dumaiss/Zephyr-80/Code/HOST/CPM2.2/docs/memory-map.md

# Zephyr-80 CP/M 2.2 Memory Map

Generated by `tools/generate_memory_docs.py` from `build/firmware.lst`, `src/layout/memory.inc`, `build/layout.manifest` and the image artifacts. Do not edit by hand; `make` regenerates it and fails if the layout breaks a rule below.

The operating system runs from SRAM bank 7, visible at `2000h-DFFFh` only in latch mode 11. Common memory, `E000h-FFFFh`, is SRAM bank 0 in both modes. See `docs/Zephyr-80_OS_Execution_Memory_Architecture.md` for the design.

## What a Program Sees (mode 10)

| Range | Use |
|---|---|
| `0000h-00FFh` | Page zero, default FCBs and default DMA, in the program's bank |
| `0100h-DFFFh` | Banked transient program area |
| `E000h-E3FFh` | Program reservation: interrupt callbacks and their data |
| `E400h-EBFFh` | CCP (ZCPR2), restored on warm boot |
| `EC00h-EC05h` | BDOS serial number |
| `EC06h` | `FBASE`, the BDOS entry |
| `F000h-FFFFh` | System common memory |

Page zero's `0006h` holds `EC06h`: the transient program area is `0100h-EC05h`, 60166 bytes (58.8 KiB).

## Common Memory

Code regions, each bounded by the limit `cbios_defs.inc` declares for it. Used and free are bytes.

| Region | Owner | Zone | Used | Free | Contents |
|---|---|---|---:|---:|---|
| `EC00h-EF9Fh` | BDOS facade | abi | 928 | 0 | `CALL 5`: serial number, `FBASE`, argument staging, Zephyr functions 200-218, system information block. |
| `EFA0h-EFB0h` | IOC link failure record | abi | 16 | 1 | Read by the CP/M tools through BDOS function 203. |
| `EFB1h-EFF7h` | Destructive COM loader | abi | 66 | 5 | Private BDOS 219: 512-byte native load, supervisor commit and close, jump to 0100h. |
| `EFF8h-EFFFh` | Transport level | abi | 1 | 7 | The BIOS IO Controller transport level byte. |
| `F000h-F1AFh` | BIOS tables, ROM copy, boot | abi | 425 | 7 | CP/M BIOS table, Zephyr extension table, reset copy, cold boot, warm-boot teardown, supervisor entry glue, page zero. |
| `F1B0h-F1D1h` | SIO ownership return | crossing | 34 | 0 | Quiesces application-owned SIO0/A at boot and application exit. |
| `F1D2h-F20Fh` | Native file gate | crossing | 46 | 16 | Function 218 descriptor and read-data staging through the existing crossing mechanism. |
| `F210h-F2E7h` | Banking services | crossing | 210 | 6 | `SELMEM`, `SETBNK`, `XMOVE`, `MOVE`. |
| `F2E8h-F307h` | Crossing layer | crossing | 26 | 6 | Mode-preserving bank select; SIO IM2 entry belongs to the IRQ core. |
| `F308h-F4EFh` | Crossing gates | crossing | 476 | 12 | Console and IOC/video gates into bank 7, inert disk entries, warm-boot trap, ROM-disk copy window, bank 7 check. |
| `F4F0h-F4FFh` | CTC reset | interrupt | 15 | 1 | `ctc_disable_interrupts`: CTC reset and vector base. |
| `F500h-F65Fh` | SIO core | interrupt | 330 | 22 | SIO0/B and SIO1 initialization, receive sinks, SIO interrupt body. |
| `F660h-F757h` | Interrupt dispatch | interrupt | 189 | 59 | CTC/SIO entries, complete context preservation, dispatch and boot policy. |
| `F758h-F79Fh` | IRQ policy | interrupt | 64 | 8 | Interrupt tokens, stackless boot policy and polling context preservation. |
| `F7A0h-F7BFh` | CTC channel mapping | interrupt | 21 | 11 | Logical-channel stop using the platform port mapping. |
| `F7C0h-F84Fh` | IRQ registration | interrupt | 121 | 23 | Atomic user/kernel callback registration. |
| `F850h-F9FFh` | Serial console | driver-isr | 84 | 348 | Serial console tee and input switch. |

Data and stacks:

| Range | Use | Notes |
|---|---|---|
| `FA00h-FBFFh` | Staging buffer | 512 bytes, shared by facade DMA/FCB/console/time staging, gate mailboxes and payloads, and cross-bank `MOVE` chunks. Users never overlap in time. |
| `FF60h (empty)` | Facade copies | Search-first FCB, DPB copy (function 31), register block (functions 210-217), ALV copy (function 27). |
| `FD00h-FDFFh` | IM2 vector page | `I` = `FDh`; programmed even entries point into common memory. |
| `FE00h` | IM2 `FFh` guard | Second byte of the pointer fetched at `FDFFh`; completes the safe `F6F6h` target. |
| `FE01h-FE7Fh` | BIOS runtime state | Bank, DMA, console, banking, storage, SIO and serial console state. |
| `FE80h-FE81h` | Interrupted SP | Saved by every interrupt entry. |
| `FE82h-FEBFh` | ISR stack | SIO and CTC interrupts; registered callbacks run here. |
| `FEC0h-FEFFh` | Gate stack | Program calls through the crossing gates. |
| `FF00h-FF5Fh` | Facade stack | BDOS facade, warm-boot trap, final boot switch to mode 10. |

System common code ends at `F8A3h`.

## SRAM Bank 7 (mode 11 only)

| Region | Owner | Zone | Used | Free | Contents |
|---|---|---|---:|---:|---|
| `2000h-2FFFh` | ZSDOS | core | — | — | Installed from `build/bdos-zsdos.bin` by `tools/split_banked_image.py`. |
| `3000h-31FFh` | ZSDOS's BIOS table | core | 59 | 453 | The table ZSDOS calls, and the `BANK7OS1` image marker. |
| `3200h-33FFh` | Console facade | core | 125 | 387 | CP/M console entries; dispatch on the console stack. |
| `3400h-35FFh` | Storage facade | core | 26 | 486 | CP/M disk entries; jumps into the drive dispatcher. |
| `3600h-37FFh` | VIDEO_SEND | core | 40 | 472 | Raw video request through the selected console backend. |
| `3800h-39FFh` | IOCALL | core | 140 | 372 | 32-byte mailbox transaction. |
| `3A00h-41FFh` | IOC command lane | driver | 1037 | 1011 | Common-packet command-lane transport. |
| `4200h-43FFh` | Bulk entries | core | 43 | 469 | `IOCBULK` and `IOCBULKW`. |
| `4400h-49FFh` | IOC bulk lane | driver | 558 | 978 | Common-packet bulk-lane transport and link bring-up. |
| `4A00h-4BFFh` | USB keyboard input | driver | 186 | 326 | Doorbell-gated keyboard fetch. |
| `4C00h-4DFFh` | USB keyboard state | state | 57 | 455 | Mailboxes and keyboard queue. |
| `4E00h-53FFh` | SD-card backend | driver | 745 | 791 | Record read and write through the IO Controller cache. |
| `5400h-55FFh` | B: select probe | driver | 23 | 489 | Card availability, then the B: DPH. |
| `5600h-57FFh` | Drive A: backend | driver | 164 | 348 | The build-selected A: backend. |
| `5800h-59FFh` | Drive dispatcher | core | 179 | 333 | Routes A: to its backend, gated B: to the synthetic FAT BIOS, and C:/D: to SD units. |
| `5A00h-5FFFh` | CP/M A: mount provider | driver | 1192 | 344 | Read-only CP/M directory/extent adapter behind function 218 at `/SYSTEM/A`. |
| `8000h-87FFh` | Console font | asset | 2048 | 0 | Build-selected CP850 glyph source, read once at boot. |
| `8800h-8BFFh` | Boot banner text | asset | 64 | 960 | Banner string, CP850 to match the console atlas. |
| `8C00h-8FFFh` | Boot banner printer | asset | 56 | 968 | Prints the banner text beside it; runs once from cold boot, in mode 11. |
| `9000h-9FFFh` | V9958 console | driver | 3208 | 888 | Direct LunchCrema V9958 console: parser, renderer, cursor and state. |
| `A000h-B7FFh` | FAT BDOS backend | driver | 5768 | 376 | FS2 client, native file manager, writable FAT BDOS personality, read cache, DPH and DPB. |
| `B800h-B9FFh` | SIO services (bank 7) | core | 121 | 391 | `sio1_ioc_init`, `sio_core_enable_interrupts`, `sio_register_rx_sink`: reached only from bank 7 or from boot after `bank7_check`. |
| `BA00h-BBFFh` | Serial console tee (bank 7) | driver | 211 | 301 | Driver table, init/install, the CONST/CONIN/CONOUT tee and TX; polled through the console facade. |
| `BE00h-BFFFh` | Transient supervisor | core | 104 | 408 | Single-foreground lifecycle policy: next program after cold boot and WBOOT teardown, default shell launch, BDOS 219 child commit. |

Data:

| Range | Use | Notes |
|---|---|---|
| `6000h` | Drive A: DPH and DPB | Build-selected A: backend. |
| `6020h` | B: DPH and DPB | SD unit 0. |
| `6040h` | Directory buffer | Shared by every drive. |
| `6100h` | Drive A: allocation vector | |
| `6300h` | B: allocation vector | |
| `6400h` | C: allocation vector | |
| `6500h` | C: DPH and DPB | SD unit 1. |
| `6510h-65FFh` | Unallocated | Deliberate gap after the C: DPH. |
| `6600h-7FFFh` | Reclaimable resource/cache pool | 13 lines of 512 bytes; no permanent owner. |
| `8000h-87FFh` | Console font | CP850 6x8. |
| `8800h-883Fh` | Boot banner text | |
| `A04Ah` | B: synthetic DPH and DPB | Read-only FAT compatibility geometry; selection gate is `1`. |

The last resident asset ends at `D649h`. Cold boot installs all 64 KiB; OS-owned initialized contents may occupy `C000h-DFFFh` outside the reservations below.

| Range | Use |
|---|---|
| `C000h-C0FFh` | Boot and warm-boot stack |
| `C100h-C1FFh` | Console and storage dispatch stack |
| `C200h-C2FFh` | IO Controller transport stack |
| `C300h-C3BFh` | SD transaction scratch (`MOVE_BUFFER`) |
| `C3C0h-C3FFh` | Unallocated |
| `C400h-CBFFh` | Pristine CCP restore asset |
| `CC00h (empty)` | Unallocated |
| `CC00h-CDFFh` | SD deblock line (one 512-byte logical block) |
| `CE00h-CE08h` | SD deblock tag (valid, unit, block) |
| `CE09h-CE0Fh` | Unallocated |
| `CE10h-D60Fh` | FAT BDOS persistent-state reservation | Fixed bank-7 state; track/sector and synthetic ALV currently use `1131` bytes. |
| `D610h-D70Fh` | CP/M A: mount state | Function-218 provider CWD, handle, iterator and extent-reader state; currently uses `58` bytes. |
| `D710h-D71Fh` | Transient supervisor state | Foreground role, execution policy, flags and layout version; currently uses `4` bytes. Written in full at cold boot. |
| `D720h-DFFFh` | Unallocated |

All eight physical SRAM banks include E000h-FFFFh, visible in flat mode 01. Modes 10/11 overlay that range with bank 0.

## Image

| Bank / page | Payload | Size | Source |
|---:|---|---:|---|
| 0 | Reset vector and common memory | 65536 | `build/firmware.bin` |
| 1 | ROM disk page 1 | 49152 | `build/romdisk.p1.bin` |
| 2 | ROM disk page 2 | 49152 | `build/romdisk.p2.bin` |
| 3 | ROM disk page 3 | 49152 | `build/romdisk.p3.bin` |
| 7 | OS bank 7 | 65536 | `build/bank7.bin` |

The burnable image `build/zephyr80.bin` is 524288 bytes. Console backend: `v9958`. Drive A: backend: `rom`. FAT drive selection gate: `1`.

## Validation Report

Status: PASS.

Checked:

- Every declared region starts at its base symbol and ends at or below its limit.
- Declared regions do not overlap.
- No assembled bytes overlap the caller window beyond the disposable bootstrap, ZSDOS, private stacks/scratch, pristine CCP, program reservation or live CCP.
- Bank 7 resident contents fit below `E000h`; the full 64 KiB boot page is installed.
- `FBASE` is six bytes into the facade, which follows the 2 KiB CCP slot; the facade ends below `CBIOS_BASE`.
- ZSDOS's BIOS table is at `ZSDOS_ORG + ZSDOS_SIZE`, and ends with the `BANK7OS1` marker.
- The CP/M BIOS table and the Zephyr extension table are jumps, in order.
- The IM2 vector page is 256 bytes at `I * 100h`; programmed even vectors and the cross-page `FFh` vector point into common memory.
- Staging buffers stay inside the shared buffer, and the returned copies do not overlap each other or the IM2 page.
- Runtime state blocks stay inside `FE00h-FE7Fh` without overlapping.
- The interrupt, gate and facade stacks are ordered, disjoint and common; the BIOS private stacks and SD scratch lie in bank 7's `C000h-DFFFh`.
- The 13-by-512-byte resource/cache pool remains reclaimable and disjoint from fixed FAT code and persistent state.
- FAT backend code and persistent state remain inside their declared bank-7 ceilings.
- The synthetic FAT DPH points at the shared directory buffer, its fixed DPB, a null CSV and its bank-7 ALV.
