dumaiss/Zephyr-80/Code/HOST/ColecoGo/snap/coleco/0000.png

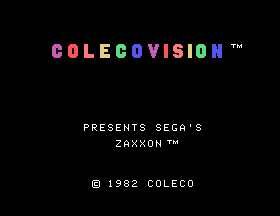
Code/HOST/ColecoGo/snap/coleco/0000.png
