dumaiss/Zephyr-80/Code/MCU/IOController/include/ioc_frame.h

#ifndef IOC_FRAME_H
#define IOC_FRAME_H

#include "sd_card.h"

#include <stdint.h>
#include <stdbool.h>

/* BIOS-facing command mailboxes remain fixed at 32 bytes.  They are no longer
 * the wire format: both SIO lanes use the common variable-length packet below,
 * and the transport maps between that packet and this compatibility mailbox.
 *
 * Layout:
 *   byte 0      class / command / response type
 *   byte 1      sequence number
 *   byte 2      status / flags
 *   byte 3      payload length (consumer-defined)
 *   bytes 4-19  payload (up to 16 bytes)
 *   bytes 20-31 reserved / command-specific
 */
#define IOC_FRAME_SIZE  32

/* Common packet used on BOTH command and bulk lanes:
 *
 *   A5 5A LEN_LO LEN_HI TYPE SEQ STATUS DATA... CRC_HI CRC_LO
 *
 * LEN counts TYPE + SEQ + STATUS + DATA.  STATUS is the first protocol
 * payload byte in both directions; requests send zero.  CRC-16-CCITT uses
 * polynomial 1021h, initial value 0000h, MSB-first processing, no final XOR,
 * and covers LEN_LO through the final DATA byte (not A5 5A).
 *
 * Keeping STATUS in every packet gives the existing mailbox a lossless mapping:
 * bytes 0/1/2 are TYPE/SEQ/STATUS, byte 3 is the derived DATA length, and bytes
 * 4.. are DATA.  Bytes 30/31 are ordinary compatibility-mailbox reserve now;
 * the transport CRC exists only on the wire. */
#define IOC_PACKET_SYNC0           0xA5u
#define IOC_PACKET_SYNC1           0x5Au
#define IOC_PACKET_FIXED_LEN       3u
#define IOC_PACKET_CRC_BYTES       2u
#define IOC_COMMAND_MAX_DATA       (IOC_FRAME_SIZE - IOC_OFF_PAYLOAD - 2u)
#define IOC_COMMAND_MAX_WIRE       (2u + 2u + IOC_PACKET_FIXED_LEN + \
                                    IOC_COMMAND_MAX_DATA + IOC_PACKET_CRC_BYTES)

/* Byte offsets within a frame */
#define IOC_OFF_CLASS    0
#define IOC_OFF_SEQ      1
#define IOC_OFF_STATUS   2
#define IOC_OFF_LEN      3
#define IOC_OFF_PAYLOAD  4

/* READY reply payload, for any command that hands off to the bulk lane.
 * Status is already frame byte 2, so the payload carries the rest:
 *
 *   byte 4  transfer id   (0 means "no transfer")
 *   byte 5  direction     (BULK_DIR_*)
 *   byte 6  length low
 *   byte 7  length high
 */
#define IOC_OFF_READY_XFER_ID    (IOC_OFF_PAYLOAD + 0u)
#define IOC_OFF_READY_DIRECTION  (IOC_OFF_PAYLOAD + 1u)
#define IOC_OFF_READY_LEN_LO     (IOC_OFF_PAYLOAD + 2u)
#define IOC_OFF_READY_LEN_HI     (IOC_OFF_PAYLOAD + 3u)
/* The LBA (or record number) the MCU actually DECODED from the request, echoed
 * back so the host can check it before any data moves.
 *
 * This began as a mitigation for a command lane with no CRC, where a false bit
 * lock could hand a handler a garbage LBA and land a write on a sector nobody
 * asked for -- silently, reporting success.  Observed at the time: the target
 * sector kept its previous contents while the write reported OK.
 *
 * The frame CRC above is now the real fix, and it is checked before dispatch.
 * The echo stays because it is nearly free and it checks a different thing: the
 * CRC proves the frame arrived intact, the echo proves the MCU and the host
 * agree on what the frame MEANT.  A decode bug on either side survives a
 * perfect CRC. */
#define IOC_OFF_READY_LBA        (IOC_OFF_PAYLOAD + 4u)
#define IOC_READY_PAYLOAD_LEN    8u

/* SD_READ_BULK request payload: 32-bit LBA, little-endian. */
#define IOC_OFF_LBA_0            (IOC_OFF_PAYLOAD + 0u)
#define IOC_SD_LBA_PAYLOAD_LEN   4u

/* SD_READ_REC / SD_WRITE_REC request payload: 32-bit CP/M record number, in the
 * same slot as the LBA so one decode path serves both.
 *
 * 8 MiB / 128 = 65536 records, so the volume needs only 16 bits today.  The
 * field is 32 anyway: it sits exactly at the 16-bit ceiling, and widening a
 * protocol field after the fact breaks every .com file already on the disk. */
#define IOC_OFF_RECORD_0         (IOC_OFF_PAYLOAD + 0u)
#define IOC_SD_RECORD_PAYLOAD_LEN 4u
#define IOC_SD_RECORD_BYTES      128u

/* XFER_STATUS REQUEST payload: which part of the raw capture window to return.
 *
 * Eight bytes of window is enough to see that a transfer went wrong and not
 * enough to say how.  A sync failure needs to be told apart three ways -- the
 * host never transmitted, the preamble is present but past the search, or the
 * preamble is corrupt -- and the first eight bytes look similar in all three.
 *
 * Byte 4 of the request is a window offset in bytes.  Zero, which every
 * existing caller sends because they zero the frame, means the same window as
 * before, so this is backward compatible. */
#define IOC_OFF_STATUS_RAW_OFF   (IOC_OFF_PAYLOAD + 0u)

/* XFER_STATUS reply payload: the DONE record. */
#define IOC_OFF_DONE_XFER_ID     (IOC_OFF_PAYLOAD + 0u)
#define IOC_OFF_DONE_STATUS      (IOC_OFF_PAYLOAD + 1u)
/* Bring-up diagnostic: the DONE reply also carries the first few bytes of the
 * transfer buffer, so a write can be checked against what the MCU actually
 * received rather than against what the card reads back afterwards.  That
 * separates "the host never sent it", "the de-shift produced garbage" and "the
 * card write went wrong", which are otherwise indistinguishable. */
#define IOC_OFF_DONE_PEEK        (IOC_OFF_PAYLOAD + 2u)
#define IOC_DONE_PEEK_BYTES      8u
/* Raw capture window, before de-shifting.  With the de-shifted peek above this
 * separates "the host never transmitted" from "the de-shift is wrong": it
 * should contain A5 5A followed by LEN/TYPE/SEQ/STATUS/DATA at some bit phase. */
#define IOC_OFF_DONE_RAW         (IOC_OFF_PAYLOAD + 2u + IOC_DONE_PEEK_BYTES)
#define IOC_DONE_RAW_BYTES       8u
/* Bulk External-Sync discriminator, valid for either transfer direction.
 *
 * DECISION is the state sampled by the most recent MCU->Z80 Bulk send:
 *   bit 0  bulk_synced was set before the send
 *   bit 1  /SYNCA LAT was idle-high before the send
 *   bit 2  the establishing setup/sync-byte path ran
 *   bit 3  /SYNCA LAT was asserted-low after that path
 *
 * LIVE is sampled while building this reply:
 *   bit 0  bulk_synced is currently set
 *   bit 1  /SYNCA LAT is currently asserted-low
 *
 * Together they distinguish a skipped edge (decision 01h), a normal attempted
 * edge (0Eh), and a flag/line disagreement without a logic analyser. */
#define IOC_OFF_DONE_BULK_SYNC_DECISION \
    (IOC_OFF_DONE_RAW + IOC_DONE_RAW_BYTES)
#define IOC_OFF_DONE_BULK_SYNC_LIVE     \
    (IOC_OFF_DONE_BULK_SYNC_DECISION + 1u)
#define IOC_DONE_PAYLOAD_LEN     (4u + IOC_DONE_PEEK_BYTES + IOC_DONE_RAW_BYTES)

/* SD_READ returns this many bytes of the block in the payload area. */
#define IOC_SD_READ_BYTES  16

/* Command class bytes (Z80 → MCU) */
#define CMD_PING             0x01
#define CMD_RESET            0x02
#define CMD_SD_READ          0x03
#define CMD_BULK_TEST        0x04
#define CMD_SD_READ_BULK     0x05
#define CMD_XFER_STATUS      0x06
#define CMD_SD_WRITE_BULK    0x07
/* Record-addressed access, served from the SD block cache.  These are what the
 * CP/M BIOS storage driver uses; the block-addressed commands above stay for
 * bring-up tools that need to bypass the cache. */
#define CMD_SD_READ_REC      0x08
#define CMD_SD_WRITE_REC     0x09
#define CMD_SD_READ_BLOCK    0x0F   /* one volume-relative 512-byte block */
#define CMD_SD_FLUSH         0x0A
#define CMD_PROFILE          0x0B
#define CMD_LINK_SYNC        0x0C
#define CMD_HID_STATUS       0x0D
#define CMD_HID_INPUT        0x0E

/* Volume management.  A CP/M image can be an ordinary file on a FAT32 card
 * rather than the raw card, and these say which and let it be swapped.
 * Neither is needed to boot: the controller auto-mounts /CPM/CPM_1.DRV as
 * unit 0 and /CPM/CPM_2.DRV as unit 1 by convention, so the default path
 * costs the BIOS nothing. */
#define CMD_VOL_MOUNT        0x10
#define CMD_VOL_INFO         0x11

/* Shared folder, for CP/M user space only.  Not a BIOS feature: these are
 * driven from a transient through the published IOCALL / IOCBULK / IOCBULKW
 * entries, exactly as IOC_SDREC.COM and HIDSTAT.COM already do.
 *
 * Every path is built by the firmware under /SHARED/ and every data command is
 * capped at 512 bytes.  Both of those are load-bearing; see fs_share.c. */
#define CMD_FS_OPENDIR       0x20
#define CMD_FS_READDIR       0x21
#define CMD_FS_OPEN          0x22
#define CMD_FS_READ          0x23
#define CMD_FS_WRITE         0x24
#define CMD_FS_CLOSE         0x25
#define CMD_FS_STAT          0x26
#define CMD_FS_DELETE        0x27
#define CMD_FS_SELFTEST      0x28

/* FS2 is the additive, root-relative filesystem service used by the bank-7
 * FAT personality and the native Zephyr file API.  The existing 20h-28h
 * /SHARED service remains unchanged. */
#define CMD_FS2_CAPS          0x30
#define CMD_FS2_GENERATION    0x31
#define CMD_FS2_RESET         0x32
#define CMD_FS2_ROOT          0x33
#define CMD_FS2_PUSH          0x34
#define CMD_FS2_OPEN_RO       0x35
#define CMD_FS2_READ          0x36
#define CMD_FS2_CLOSE         0x37
#define CMD_FS2_OPENDIR       0x38
#define CMD_FS2_READDIR       0x39
#define CMD_FS2_CLOSEDIR      0x3A
#define CMD_FS2_STAT          0x3B
#define CMD_FS2_SPACE         0x3C
#define CMD_FS2_OPEN_RW       0x3D
#define CMD_FS2_WRITE         0x3E
#define CMD_FS2_SYNC          0x3F
#define CMD_FS2_TRUNCATE      0x40
#define CMD_FS2_UNLINK        0x41
#define CMD_FS2_RENAME        0x42
#define CMD_FS2_MKDIR         0x43
#define CMD_FS2_RMDIR         0x44

/* Response class bytes (MCU → Z80) */
#define RSP_PING             0x81
#define RSP_SD_READ          0x83
#define RSP_BULK_TEST        0x84
#define RSP_SD_READ_BULK     0x85
#define RSP_XFER_STATUS      0x86
#define RSP_SD_WRITE_BULK    0x87
#define RSP_SD_READ_REC      0x88
#define RSP_SD_WRITE_REC     0x89
#define RSP_SD_READ_BLOCK    0x8F
#define RSP_SD_FLUSH         0x8A
#define RSP_PROFILE          0x8B
#define RSP_LINK_SYNC        0x8C
#define RSP_HID_STATUS       0x8D
#define RSP_HID_INPUT        0x8E
#define RSP_VOL_MOUNT        0x90
#define RSP_VOL_INFO         0x91
#define RSP_FS_OPENDIR       0xA0
#define RSP_FS_READDIR       0xA1
#define RSP_FS_OPEN          0xA2
#define RSP_FS_READ          0xA3
#define RSP_FS_WRITE         0xA4
#define RSP_FS_CLOSE         0xA5
#define RSP_FS_STAT          0xA6
#define RSP_FS_DELETE        0xA7
#define RSP_FS_SELFTEST      0xA8
#define RSP_FS2_CAPS         0xB0
#define RSP_FS2_GENERATION   0xB1
#define RSP_FS2_RESET        0xB2
#define RSP_FS2_ROOT         0xB3
#define RSP_FS2_PUSH         0xB4
#define RSP_FS2_OPEN_RO      0xB5
#define RSP_FS2_READ         0xB6
#define RSP_FS2_CLOSE        0xB7
#define RSP_FS2_OPENDIR      0xB8
#define RSP_FS2_READDIR      0xB9
#define RSP_FS2_CLOSEDIR     0xBA
#define RSP_FS2_STAT         0xBB
#define RSP_FS2_SPACE        0xBC
#define RSP_FS2_OPEN_RW      0xBD
#define RSP_FS2_WRITE        0xBE
#define RSP_FS2_SYNC         0xBF
#define RSP_FS2_TRUNCATE     0xC0
#define RSP_FS2_UNLINK       0xC1
#define RSP_FS2_RENAME       0xC2
#define RSP_FS2_MKDIR        0xC3
#define RSP_FS2_RMDIR        0xC4

/* ---------------------------------------------------------------------------
 * FS2 capability contract (version 1)
 * ---------------------------------------------------------------------------
 *
 * Two FIL slots, one DIR slot, one bounded component resolver and the existing
 * 512-byte bulk staging buffer.  Counts and limits are reported so later pool
 * growth does not change the ABI.  Generation covers media/context
 * invalidation while the Z80 keeps running.  An MCU reset resets the whole
 * machine, so there is no boot nonce.
 */
#define IOC_FS2_VERSION                  1u
#define IOC_FS2_STATUS_VERSION           1u
#define IOC_FS2_TOKEN_BYTES              2u
#define IOC_FS2_CHUNK_MAX                512u
#define IOC_FS2_FILE_SLOTS               2u
#define IOC_FS2_DIR_SLOTS                1u
#define IOC_FS2_RESOLVER_COMPONENTS      16u

#define IOC_FS2_CAP_READ_ONLY            0x0001u
#define IOC_FS2_CAP_EXPLICIT_OFFSET      0x0002u
#define IOC_FS2_CAP_COMPONENT_RESOLVER   0x0004u
#define IOC_FS2_CAP_MEDIA_GENERATION     0x0008u
#define IOC_FS2_CAP_STAT                 0x0010u
#define IOC_FS2_CAP_SPACE                0x0020u
#define IOC_FS2_CAP_WRITE                0x0040u
#define IOC_FS2_CAP_TRUNCATE             0x0080u
#define IOC_FS2_CAP_UNLINK               0x0100u
#define IOC_FS2_CAP_RENAME               0x0200u
#define IOC_FS2_CAP_MKDIR                0x0400u
#define IOC_FS2_CAP_RMDIR                0x0800u

/* RSP_FS2_CAPS payload.  Multibyte fields are little-endian. */
#define IOC_OFF_FS2_CAP_VERSION          (IOC_OFF_PAYLOAD + 0u)
#define IOC_OFF_FS2_CAP_STATUS_VERSION   (IOC_OFF_PAYLOAD + 1u)
#define IOC_OFF_FS2_CAP_FLAGS            (IOC_OFF_PAYLOAD + 2u)  /* uint16 */
#define IOC_OFF_FS2_CAP_GENERATION       (IOC_OFF_PAYLOAD + 4u)  /* uint32 */
#define IOC_OFF_FS2_CAP_CHUNK_MAX        (IOC_OFF_PAYLOAD + 8u)  /* uint16 */
#define IOC_OFF_FS2_CAP_FILE_SLOTS       (IOC_OFF_PAYLOAD + 10u)
#define IOC_OFF_FS2_CAP_DIR_SLOTS        (IOC_OFF_PAYLOAD + 11u)
#define IOC_OFF_FS2_CAP_RESOLVER_MAX     (IOC_OFF_PAYLOAD + 12u)
#define IOC_OFF_FS2_CAP_TOKEN_BYTES      (IOC_OFF_PAYLOAD + 13u)
#define IOC_FS2_CAP_REPLY_LEN            14u

/* RSP_FS2_GENERATION carries only the current uint32 media generation. */
#define IOC_OFF_FS2_GENERATION           (IOC_OFF_PAYLOAD + 0u)
#define IOC_FS2_GENERATION_REPLY_LEN     4u

/* FS2 request and reply layouts.  Every name is the same packed, space-padded
 * 8.3 form used by an FCB.  Tokens are little-endian slot/cookie values and
 * are meaningful only to the command which issued them. */
#define IOC_OFF_FS2_NAME                 (IOC_OFF_PAYLOAD + 0u) /* 11 bytes */
#define IOC_FS2_NAME_REQ_LEN             IOC_NAME_LEN

/* OPEN_RW request: one mode byte followed by the packed name. */
#define IOC_OFF_FS2_OPEN_MODE            (IOC_OFF_PAYLOAD + 0u)
#define IOC_OFF_FS2_OPEN_NAME            (IOC_OFF_PAYLOAD + 1u)
#define IOC_FS2_OPEN_RW_REQ_LEN          (1u + IOC_NAME_LEN)
#define IOC_FS2_OPEN_UPDATE              0u
#define IOC_FS2_OPEN_CREATE_NEW          1u
#define IOC_FS2_OPEN_CREATE_ALWAYS       2u

#define IOC_OFF_FS2_TOKEN                (IOC_OFF_PAYLOAD + 0u) /* uint16 */
#define IOC_OFF_FS2_OFFSET               (IOC_OFF_PAYLOAD + 2u) /* uint32 */
#define IOC_OFF_FS2_LENGTH               (IOC_OFF_PAYLOAD + 6u) /* uint16 */
#define IOC_FS2_READ_REQ_LEN              8u
#define IOC_FS2_WRITE_REQ_LEN             IOC_FS2_READ_REQ_LEN

#define IOC_OFF_FS2_TRUNCATE_SIZE         (IOC_OFF_PAYLOAD + 2u) /* uint32 */
#define IOC_FS2_TRUNCATE_REQ_LEN           6u

/* UNLINK, MKDIR and RMDIR take a single packed name at IOC_OFF_FS2_NAME and
 * reply with no payload.  RENAME takes the existing name followed by the new
 * one; both are resolved against the same current resolver path, so this is a
 * rename within one directory and never a cross-directory move. */
#define IOC_OFF_FS2_RENAME_FROM          (IOC_OFF_PAYLOAD + 0u) /* 11 bytes */
#define IOC_OFF_FS2_RENAME_TO            (IOC_OFF_PAYLOAD + IOC_NAME_LEN)
#define IOC_FS2_RENAME_REQ_LEN           (2u * IOC_NAME_LEN)

#define IOC_OFF_FS2_OPEN_TOKEN           (IOC_OFF_PAYLOAD + 0u) /* uint16 */
#define IOC_OFF_FS2_OPEN_SIZE            (IOC_OFF_PAYLOAD + 2u) /* uint32 */
#define IOC_OFF_FS2_OPEN_ATTR            (IOC_OFF_PAYLOAD + 6u) /* reserved, zero */
#define IOC_FS2_OPEN_REPLY_LEN            7u

#define IOC_OFF_FS2_DIR_TOKEN            (IOC_OFF_PAYLOAD + 0u) /* uint16 */
#define IOC_FS2_DIR_REPLY_LEN             2u
#define IOC_OFF_FS2_DIRENT_NAME          (IOC_OFF_PAYLOAD + 0u) /* 11 bytes */
#define IOC_OFF_FS2_DIRENT_ATTR          (IOC_OFF_PAYLOAD + 11u) /* AM_DIR only */
#define IOC_OFF_FS2_DIRENT_SIZE          (IOC_OFF_PAYLOAD + 12u) /* uint32 */
#define IOC_FS2_DIRENT_REPLY_LEN         16u

#define IOC_OFF_FS2_STAT_SIZE            (IOC_OFF_PAYLOAD + 0u) /* uint32 */
#define IOC_OFF_FS2_STAT_ATTR            (IOC_OFF_PAYLOAD + 4u) /* AM_DIR only */
#define IOC_FS2_STAT_REPLY_LEN            5u
#define IOC_OFF_FS2_SPACE_FREE           (IOC_OFF_PAYLOAD + 0u) /* legacy saturated bytes */
#define IOC_OFF_FS2_SPACE_TOTAL          (IOC_OFF_PAYLOAD + 4u) /* legacy saturated bytes */
#define IOC_OFF_FS2_SPACE_FREE_KIB       (IOC_OFF_PAYLOAD + 8u) /* exact uint32 KiB */
#define IOC_OFF_FS2_SPACE_TOTAL_KIB      (IOC_OFF_PAYLOAD + 12u) /* exact uint32 KiB */
#define IOC_FS2_SPACE_REPLY_LEN           16u

/* ---------------------------------------------------------------------------
 * Volume commands
 * ---------------------------------------------------------------------------
 *
 * Names are packed 8.3 throughout -- eleven bytes, space padded, no dot.  That
 * is the FCB layout, so a transient drops a reply straight into an FCB and a
 * request straight out of one, with no parsing on the Z80 at all.
 */
#define IOC_NAME_LEN               11u

/* CMD_VOL_MOUNT request: unit, then the packed name. */
#define IOC_OFF_VOL_REQ_UNIT       (IOC_OFF_PAYLOAD + 0u)
#define IOC_OFF_VOL_REQ_NAME       (IOC_OFF_PAYLOAD + 1u)
#define IOC_VOL_MOUNT_REQ_LEN      (1u + IOC_NAME_LEN)

/* Reply to both volume commands: what is mounted on that unit. */
#define IOC_OFF_VOL_UNIT           (IOC_OFF_PAYLOAD + 0u)
#define IOC_OFF_VOL_MODE           (IOC_OFF_PAYLOAD + 1u)
#define IOC_OFF_VOL_EXTENTS        (IOC_OFF_PAYLOAD + 2u)
#define IOC_OFF_VOL_BASE_LBA       (IOC_OFF_PAYLOAD + 3u)   /* 4 bytes, LE */
#define IOC_OFF_VOL_RECORDS        (IOC_OFF_PAYLOAD + 7u)   /* 4 bytes, LE */
#define IOC_OFF_VOL_NAME           (IOC_OFF_PAYLOAD + 11u)  /* 11 bytes */
/* Boot-guard state, so a degraded controller says so rather than just looking
 * like a card with no filesystem.  See boot_guard.h. */
#define IOC_OFF_VOL_GUARD          (IOC_OFF_PAYLOAD + 22u)
#define IOC_OFF_VOL_RESETS         (IOC_OFF_PAYLOAD + 23u)
#define IOC_OFF_VOL_STKRST         (IOC_OFF_PAYLOAD + 24u)
#define IOC_VOL_INFO_LEN           25u

/* Mode byte, matching VolMode.  Reported rather than inferred: a host must be
 * able to tell a file-backed volume from the raw card without guessing. */
#define IOC_VOL_MODE_NONE          0x00u
#define IOC_VOL_MODE_RAW           0x01u
#define IOC_VOL_MODE_FILE          0x02u

/* ---------------------------------------------------------------------------
 * Optional unit byte on the record commands
 * ---------------------------------------------------------------------------
 *
 * It lands at payload offset 4, immediately after the 32-bit record, which the
 * 32-byte mailbox has ample room for.  The firmware reads it only when the
 * frame's LEN is 5 or more and defaults to unit 0 otherwise -- so a BIOS built
 * before volumes existed keeps working against unit 0 with no edit at all.
 */
#define IOC_OFF_RECORD_UNIT        (IOC_OFF_PAYLOAD + 4u)
#define IOC_SD_RECORD_UNIT_LEN     5u

/* ---------------------------------------------------------------------------
 * Shared-folder commands
 * ---------------------------------------------------------------------------
 *
 * Read and write carry an explicit offset.  Four bytes out of a payload with
 * room for twenty-six, and it is what makes a transfer idempotent: with an
 * implicit file position a retried transaction -- which this link does -- would
 * silently advance twice and corrupt the copy somewhere in the middle.
 */
#define IOC_FS_CHUNK_MAX           512u

/* Request layouts */
#define IOC_OFF_FS_NAME            (IOC_OFF_PAYLOAD + 0u)   /* 11 bytes */
#define IOC_OFF_FS_OPEN_MODE       (IOC_OFF_PAYLOAD + 0u)
#define IOC_OFF_FS_OPEN_NAME       (IOC_OFF_PAYLOAD + 1u)
#define IOC_OFF_FS_XFER_HANDLE     (IOC_OFF_PAYLOAD + 0u)
#define IOC_OFF_FS_XFER_OFFSET     (IOC_OFF_PAYLOAD + 1u)   /* 4 bytes, LE */
#define IOC_OFF_FS_XFER_LEN        (IOC_OFF_PAYLOAD + 5u)   /* 2 bytes, LE */
#define IOC_OFF_FS_CLOSE_HANDLE    (IOC_OFF_PAYLOAD + 0u)
#define IOC_OFF_FS_CLOSE_SIZE      (IOC_OFF_PAYLOAD + 1u)   /* 4 bytes, LE */

/* CMD_FS_OPEN mode byte */
#define IOC_FS_MODE_READ           0x00u
#define IOC_FS_MODE_WRITE          0x01u   /* create, truncate */

/* CMD_FS_READDIR reply */
#define IOC_OFF_FS_DIR_NAME        (IOC_OFF_PAYLOAD + 0u)   /* 11 bytes */
#define IOC_OFF_FS_DIR_ATTR        (IOC_OFF_PAYLOAD + 11u)
#define IOC_OFF_FS_DIR_SIZE        (IOC_OFF_PAYLOAD + 12u)  /* 4 bytes, LE */
#define IOC_OFF_FS_DIR_MORE        (IOC_OFF_PAYLOAD + 16u)
#define IOC_FS_READDIR_LEN         17u

/* CMD_FS_OPEN / CMD_FS_STAT reply */
#define IOC_OFF_FS_OPEN_HANDLE     (IOC_OFF_PAYLOAD + 0u)
#define IOC_OFF_FS_OPEN_SIZE       (IOC_OFF_PAYLOAD + 1u)   /* 4 bytes, LE */
#define IOC_FS_OPEN_REPLY_LEN      5u
#define IOC_OFF_FS_STAT_SIZE       (IOC_OFF_PAYLOAD + 0u)   /* 4 bytes, LE */
#define IOC_OFF_FS_STAT_ATTR       (IOC_OFF_PAYLOAD + 4u)
#define IOC_FS_STAT_REPLY_LEN      5u

/* CMD_FS_SELFTEST reply: what the mount found, and a checksum of a known file.
 * Cheap insurance against XC8's overlay allocator -- run it before trusting
 * any of this on hardware.  See the risk section of the design document. */
#define IOC_OFF_FS_SELF_MOUNTED    (IOC_OFF_PAYLOAD + 0u)
#define IOC_OFF_FS_SELF_FSTYPE     (IOC_OFF_PAYLOAD + 1u)
#define IOC_OFF_FS_SELF_CSIZE      (IOC_OFF_PAYLOAD + 2u)   /* 2 bytes, LE */
#define IOC_OFF_FS_SELF_DATABASE   (IOC_OFF_PAYLOAD + 4u)   /* 4 bytes, LE */
#define IOC_OFF_FS_SELF_FILES      (IOC_OFF_PAYLOAD + 8u)   /* 2 bytes, LE */
#define IOC_OFF_FS_SELF_SUM        (IOC_OFF_PAYLOAD + 10u)  /* 2 bytes, LE */
#define IOC_OFF_FS_SELF_BYTES      (IOC_OFF_PAYLOAD + 12u)  /* 4 bytes, LE */
#define IOC_OFF_FS_SELF_FRESULT    (IOC_OFF_PAYLOAD + 16u)
#define IOC_FS_SELFTEST_LEN        17u

/* HID_INPUT is a nonblocking terminal-input dequeue.  The request payload is
 * one byte: the maximum number of bytes wanted (0 is a status-only query).
 * Replies carry the number still queued, the saturating count of dropped key
 * sequences, then up to 24 translated terminal bytes. */
#define IOC_OFF_HID_INPUT_MAX       IOC_OFF_PAYLOAD
#define IOC_OFF_HID_INPUT_QUEUED    (IOC_OFF_PAYLOAD + 0u)
#define IOC_OFF_HID_INPUT_DROPPED   (IOC_OFF_PAYLOAD + 1u)
#define IOC_OFF_HID_INPUT_DATA      (IOC_OFF_PAYLOAD + 2u)
#define IOC_HID_INPUT_MAX_DATA      (IOC_COMMAND_MAX_DATA - 2u)
#define IOC_HID_INPUT_META_LEN      2u

/* HID_STATUS reply payload.  /USB_INT is reported as the raw pin level so a
 * low asserted interrupt remains visible even though this bring-up phase does
 * not dispatch it. */
#define IOC_OFF_HID_STATUS         (IOC_OFF_PAYLOAD + 0u)
#define IOC_OFF_HID_REVISION       (IOC_OFF_PAYLOAD + 1u)
#define IOC_OFF_HID_USB_INT        (IOC_OFF_PAYLOAD + 2u)
#define IOC_OFF_HID_REV_125KHZ     (IOC_OFF_PAYLOAD + 3u)
#define IOC_OFF_HID_REV_1MHZ       (IOC_OFF_PAYLOAD + 4u)
#define IOC_OFF_HID_REV_4MHZ       (IOC_OFF_PAYLOAD + 5u)
/* GPOUT write/read-back link test, one result per rate.  00h passes; FFh means
 * the PIC's SPI module never completed a byte; otherwise a mask of the GPOUT
 * bits that read back wrong.  See ioc_hid.h for how to read the pattern. */
#define IOC_OFF_HID_GPOUT_125KHZ   (IOC_OFF_PAYLOAD + 6u)
#define IOC_OFF_HID_GPOUT_1MHZ     (IOC_OFF_PAYLOAD + 7u)
#define IOC_OFF_HID_GPOUT_4MHZ     (IOC_OFF_PAYLOAD + 8u)
#define IOC_HID_GPOUT_XFER_ERROR   0xFFu
/* Blind command-path test on the /USB_INT pin, which needs no MISO.  Bit 0 is
 * the pin with PINCTL.POSINT clear (expect 1), bit 1 with POSINT set (expect
 * 0).  01h passes; 03h is stuck high, meaning nothing reaches the part. */
#define IOC_OFF_HID_INT_DRIVE      (IOC_OFF_PAYLOAD + 9u)
#define IOC_HID_INT_DRIVE_PASS     0x01u
/* Link quality: how many of the 64 reads in each revision burst produced the
 * winning revision code.  40h is a clean bus, 00h is nothing legal at all, and
 * anything between is a marginal connection.  The revision byte alone cannot
 * distinguish a good bus from a lucky sample. */
#define IOC_OFF_HID_MATCH_125KHZ   (IOC_OFF_PAYLOAD + 10u)
#define IOC_OFF_HID_MATCH_1MHZ     (IOC_OFF_PAYLOAD + 11u)
#define IOC_OFF_HID_MATCH_4MHZ     (IOC_OFF_PAYLOAD + 12u)
#define IOC_HID_PROBE_READS        64u
/* Live USB state.  DEV_COUNT is devices currently mounted; KBD_ADDR is 0 when
 * no keyboard is present.  REPORTS is a 16-bit little-endian count of boot
 * reports received since mount, and LAST is that report: modifier, reserved,
 * then six keycodes. */
#define IOC_OFF_HID_DEV_COUNT      (IOC_OFF_PAYLOAD + 13u)
#define IOC_OFF_HID_KBD_ADDR       (IOC_OFF_PAYLOAD + 14u)
#define IOC_OFF_HID_REPORTS_LO     (IOC_OFF_PAYLOAD + 15u)
#define IOC_OFF_HID_REPORTS_HI     (IOC_OFF_PAYLOAD + 16u)
#define IOC_OFF_HID_LAST_REPORT    (IOC_OFF_PAYLOAD + 17u)
#define IOC_HID_LAST_REPORT_LEN    8u
/* Device speed, which on this board predicts whether the device can work at
 * all: there is an FE1.1S hub in front of every port and the MAX3421E driver
 * has no PRE-packet support, so low-speed devices behind it are unreachable.
 * 00h full, 01h low, FFh unknown. */
#define IOC_OFF_HID_KBD_SPEED      (IOC_OFF_PAYLOAD + 25u)
#define IOC_HID_SPEED_FULL         0x00u
#define IOC_HID_SPEED_LOW          0x01u
#define IOC_HID_STATUS_PAYLOAD_LEN 26u

/* CMD_HID_STATUS request selects a reply page, like CMD_PROFILE does.  Page 0
 * is the bring-up snapshot above; page 1 is raw controller/stack state, for
 * separating "nothing ever connected" from "connected but never enumerated". */
#define IOC_OFF_HID_REQ_PAGE       IOC_OFF_PAYLOAD
#define IOC_HID_PAGE_STATUS        0x00u
#define IOC_HID_PAGE_USB           0x01u
#define IOC_HID_PAGE_XFER          0x02u
#define IOC_HID_PAGE_HUB           0x03u
#define IOC_HID_PAGE_ENUM          0x04u
#define IOC_HID_PAGE_HIDCFG        0x05u
#define IOC_HID_PAGE_GAMEPAD       0x06u

/* Page 6: stable passive gamepad enumeration state, available in normal and
 * diagnostic firmware.  Unlike pages 1-5, reading it performs no active probe
 * and depends on no temporary TinyUSB internal trace.  DEVICES and LAST_* are
 * derived from TinyUSB's live non-hub address table; MOUNTS/UNMOUNTS count the
 * optional generic callbacks separately. */
#define IOC_OFF_HIDPAD_PAGE         (IOC_OFF_PAYLOAD + 0u)
#define IOC_OFF_HIDPAD_DEVICES      (IOC_OFF_PAYLOAD + 1u)
#define IOC_OFF_HIDPAD_MOUNTS       (IOC_OFF_PAYLOAD + 2u)
#define IOC_OFF_HIDPAD_UNMOUNTS     (IOC_OFF_PAYLOAD + 3u)
#define IOC_OFF_HIDPAD_LAST_ADDR    (IOC_OFF_PAYLOAD + 4u)
#define IOC_OFF_HIDPAD_LAST_VID_LO  (IOC_OFF_PAYLOAD + 5u)
#define IOC_OFF_HIDPAD_LAST_VID_HI  (IOC_OFF_PAYLOAD + 6u)
#define IOC_OFF_HIDPAD_LAST_PID_LO  (IOC_OFF_PAYLOAD + 7u)
#define IOC_OFF_HIDPAD_LAST_PID_HI  (IOC_OFF_PAYLOAD + 8u)
#define IOC_OFF_HIDPAD_HID_MOUNTS   (IOC_OFF_PAYLOAD + 9u)
#define IOC_OFF_HIDPAD_LAST_HID_ADDR (IOC_OFF_PAYLOAD + 10u)
/* Seven bytes per controller: address, instance, first-arm result, 16-bit
 * report count, last report length and current decoded latch byte. */
#define IOC_OFF_HIDPAD_PAD0_ADDR    (IOC_OFF_PAYLOAD + 11u)
#define IOC_OFF_HIDPAD_PAD0_INST    (IOC_OFF_PAYLOAD + 12u)
#define IOC_OFF_HIDPAD_PAD0_ARM     (IOC_OFF_PAYLOAD + 13u)
#define IOC_OFF_HIDPAD_PAD0_RPT_LO  (IOC_OFF_PAYLOAD + 14u)
#define IOC_OFF_HIDPAD_PAD0_RPT_HI  (IOC_OFF_PAYLOAD + 15u)
#define IOC_OFF_HIDPAD_PAD0_LEN     (IOC_OFF_PAYLOAD + 16u)
#define IOC_OFF_HIDPAD_PAD0_LATCH   (IOC_OFF_PAYLOAD + 17u)
#define IOC_OFF_HIDPAD_PAD1_ADDR    (IOC_OFF_PAYLOAD + 18u)
#define IOC_OFF_HIDPAD_PAD1_INST    (IOC_OFF_PAYLOAD + 19u)
#define IOC_OFF_HIDPAD_PAD1_ARM     (IOC_OFF_PAYLOAD + 20u)
#define IOC_OFF_HIDPAD_PAD1_RPT_LO  (IOC_OFF_PAYLOAD + 21u)
#define IOC_OFF_HIDPAD_PAD1_RPT_HI  (IOC_OFF_PAYLOAD + 22u)
#define IOC_OFF_HIDPAD_PAD1_LEN     (IOC_OFF_PAYLOAD + 23u)
#define IOC_OFF_HIDPAD_PAD1_LATCH   (IOC_OFF_PAYLOAD + 24u)
#define IOC_OFF_HIDPAD_LAST_HID_PROTO (IOC_OFF_PAYLOAD + 25u)
#define IOC_HID_GAMEPAD_PAYLOAD_LEN 26u

#define IOC_OFF_HIDDBG_PAGE        (IOC_OFF_PAYLOAD + 0u)
#define IOC_OFF_HIDDBG_TASK_LO     (IOC_OFF_PAYLOAD + 1u)
#define IOC_OFF_HIDDBG_TASK_HI     (IOC_OFF_PAYLOAD + 2u)
#define IOC_OFF_HIDDBG_INTS_LO     (IOC_OFF_PAYLOAD + 3u)
#define IOC_OFF_HIDDBG_INTS_HI     (IOC_OFF_PAYLOAD + 4u)
#define IOC_OFF_HIDDBG_DEVICES     (IOC_OFF_PAYLOAD + 5u)
#define IOC_OFF_HIDDBG_INT_LEVEL   (IOC_OFF_PAYLOAD + 6u)
#define IOC_OFF_HIDDBG_CONNECTED   (IOC_OFF_PAYLOAD + 7u)
#define IOC_OFF_HIDDBG_SPEED       (IOC_OFF_PAYLOAD + 8u)
#define IOC_OFF_HIDDBG_HIRQ        (IOC_OFF_PAYLOAD + 9u)
#define IOC_OFF_HIDDBG_MODE        (IOC_OFF_PAYLOAD + 10u)
#define IOC_OFF_HIDDBG_HRSL        (IOC_OFF_PAYLOAD + 11u)
#define IOC_OFF_HIDDBG_USBIRQ      (IOC_OFF_PAYLOAD + 12u)
#define IOC_OFF_HIDDBG_MOUNTED     (IOC_OFF_PAYLOAD + 13u)
#define IOC_OFF_HIDDBG_EV_ATTACH   (IOC_OFF_PAYLOAD + 14u)
#define IOC_OFF_HIDDBG_EV_REMOVE   (IOC_OFF_PAYLOAD + 15u)
#define IOC_OFF_HIDDBG_DEV_DESC    (IOC_OFF_PAYLOAD + 16u)
#define IOC_OFF_HIDDBG_CFG_DESC    (IOC_OFF_PAYLOAD + 17u)
#define IOC_OFF_HIDDBG_ENUM_STATE  (IOC_OFF_PAYLOAD + 18u)
#define IOC_OFF_HIDDBG_ENUM_FAILS  (IOC_OFF_PAYLOAD + 19u)
#define IOC_OFF_HIDDBG_CTRL_REJ    (IOC_OFF_PAYLOAD + 20u)
#define IOC_OFF_HIDDBG_HXFRDN      (IOC_OFF_PAYLOAD + 21u)
#define IOC_OFF_HIDDBG_XFERDONE    (IOC_OFF_PAYLOAD + 22u)
#define IOC_OFF_HIDDBG_EPNULL      (IOC_OFF_PAYLOAD + 23u)
#define IOC_OFF_HIDDBG_LASTHRSL    (IOC_OFF_PAYLOAD + 24u)
#define IOC_OFF_HIDDBG_SETUP_XFER  (IOC_OFF_PAYLOAD + 25u)
/* At the transport's ceiling: IOC_COMMAND_MAX_DATA is 26. */
#define IOC_HID_USB_PAYLOAD_LEN    26u

/* Page 2: the state handle_xfer_done() branched on.  Page 1 is full -- the
 * transport caps a reply at IOC_COMMAND_MAX_DATA -- so this is a second page
 * rather than evidence deleted to make room. */
#define IOC_OFF_HIDX_PAGE          (IOC_OFF_PAYLOAD + 0u)
#define IOC_OFF_HIDX_HXFR          (IOC_OFF_PAYLOAD + 1u)
#define IOC_OFF_HIDX_EPDIR         (IOC_OFF_PAYLOAD + 2u)
#define IOC_OFF_HIDX_PERADDR       (IOC_OFF_PAYLOAD + 3u)
#define IOC_OFF_HIDX_EPNUM         (IOC_OFF_PAYLOAD + 4u)
#define IOC_OFF_HIDX_PKTSIZE       (IOC_OFF_PAYLOAD + 5u)
#define IOC_OFF_HIDX_TOTAL_LO      (IOC_OFF_PAYLOAD + 6u)
#define IOC_OFF_HIDX_TOTAL_HI      (IOC_OFF_PAYLOAD + 7u)
#define IOC_OFF_HIDX_XFERRED_LO    (IOC_OFF_PAYLOAD + 8u)
#define IOC_OFF_HIDX_XFERRED_HI    (IOC_OFF_PAYLOAD + 9u)
#define IOC_OFF_HIDX_EPSTATE       (IOC_OFF_PAYLOAD + 10u)
#define IOC_OFF_HIDX_XACTLEN       (IOC_OFF_PAYLOAD + 11u)
/* 1 = completed (OUT/SETUP), 2 = took xact_out, 3 = re-issued HXFR (IN),
 * 4 = completed (IN), 0 = the branch was never reached. */
#define IOC_OFF_HIDX_BRANCH        (IOC_OFF_PAYLOAD + 12u)
#define IOC_OFF_HIDX_HUB_OPEN_EP   (IOC_OFF_PAYLOAD + 13u)
#define IOC_OFF_HIDX_HUB_PRE_EP    (IOC_OFF_PAYLOAD + 14u)
#define IOC_OFF_HIDX_HUB_AFTER_OPEN (IOC_OFF_PAYLOAD + 15u)
#define IOC_OFF_HIDX_SUBMIT_ADDR   (IOC_OFF_PAYLOAD + 16u)
#define IOC_OFF_HIDX_SUBMIT_EP     (IOC_OFF_PAYLOAD + 17u)
#define IOC_OFF_HIDX_SETUP         (IOC_OFF_PAYLOAD + 18u)
#define IOC_HID_XFER_PAYLOAD_LEN   26u

/* Page 3: page byte followed by the 25-byte hub lifecycle trace. */
#define IOC_OFF_HIDH_PAGE          (IOC_OFF_PAYLOAD + 0u)
#define IOC_OFF_HIDH_TRACE         (IOC_OFF_PAYLOAD + 1u)
#define IOC_HID_HUB_TRACE_LEN      25u
#define IOC_HID_HUB_PAYLOAD_LEN    26u

/* Page 4: downstream enumeration entry.  RET is FFh if the behind-hub branch
 * of enum_new_device() was never reached, FEh if it was reached but hub_port
 * was zero, 00h if hub_port_get_status() refused, 01h if it accepted. */
#define IOC_OFF_HIDE_PAGE          (IOC_OFF_PAYLOAD + 0u)
#define IOC_OFF_HIDE_CALLS         (IOC_OFF_PAYLOAD + 1u)
#define IOC_OFF_HIDE_HUB_ADDR      (IOC_OFF_PAYLOAD + 2u)
#define IOC_OFF_HIDE_HUB_PORT      (IOC_OFF_PAYLOAD + 3u)
#define IOC_OFF_HIDE_RET           (IOC_OFF_PAYLOAD + 4u)
/* ENUMERATING is the live _usbh_data.enumerating_daddr.  FFh means idle and
 * ready for a new attach; anything else means the attach path defers and
 * re-queues, which presents as an unbounded attach count. */
#define IOC_OFF_HIDE_ENUMERATING   (IOC_OFF_PAYLOAD + 5u)
#define IOC_OFF_HIDE_DEFERS        (IOC_OFF_PAYLOAD + 6u)
#define IOC_OFF_HIDE_COMPLETES     (IOC_OFF_PAYLOAD + 7u)
#define IOC_OFF_HIDE_ATT_ADDR      (IOC_OFF_PAYLOAD + 8u)
#define IOC_OFF_HIDE_ATT_PORT      (IOC_OFF_PAYLOAD + 9u)
/* Host-controller stall state.  BUSY is _hcd_data.busy_lock; EPSTATE and
 * EPPKT are the hub's interrupt-IN endpoint (addr 3, ep 1, IN).  State 03h is
 * EP_STATE_ATTEMPT_1 -- armed but never started, and the FRAME retry ignores
 * it because that test is strictly greater than ATTEMPT_1. */
#define IOC_OFF_HIDE_BUSY          (IOC_OFF_PAYLOAD + 10u)
#define IOC_OFF_HIDE_EPSTATE       (IOC_OFF_PAYLOAD + 11u)
#define IOC_OFF_HIDE_EPPKT         (IOC_OFF_PAYLOAD + 12u)
/* Hub class-driver dispatch.  CBCALLS is hub_xfer_cb() entries -- zero means
 * the completed status transfer never reached the hub driver at all.  ARMCALLS
 * is hub_edpt_status_xfer() calls.  CHANGE is the last status-change byte. */
#define IOC_OFF_HIDE_HUBCB         (IOC_OFF_PAYLOAD + 13u)
#define IOC_OFF_HIDE_HUBARM        (IOC_OFF_PAYLOAD + 14u)
#define IOC_OFF_HIDE_HUBCHANGE     (IOC_OFF_PAYLOAD + 15u)
/* Endpoint table: allocation failures, slots in use, slots total. */
#define IOC_OFF_HIDE_EPFAIL        (IOC_OFF_PAYLOAD + 16u)
#define IOC_OFF_HIDE_EPUSED        (IOC_OFF_PAYLOAD + 17u)
#define IOC_OFF_HIDE_EPTOTAL       (IOC_OFF_PAYLOAD + 18u)
/* Endpoint-to-driver binding.  EP2DRV is dev(3)->ep2drv[1][IN]: FFh means the
 * endpoint was never bound to a class driver, so its completions are dropped.
 * FEh means no such device. */
#define IOC_OFF_HIDE_EP2DRV        (IOC_OFF_PAYLOAD + 19u)
#define IOC_OFF_HIDE_BINDCALLS     (IOC_OFF_PAYLOAD + 20u)
#define IOC_OFF_HIDE_BINDDRVID     (IOC_OFF_PAYLOAD + 21u)
#define IOC_OFF_HIDE_BINDLEN_LO    (IOC_OFF_PAYLOAD + 22u)
#define IOC_OFF_HIDE_BINDLEN_HI    (IOC_OFF_PAYLOAD + 23u)
/* Set when desc_itf did not survive a nested driver->open() call. */
#define IOC_OFF_HIDE_ITFCLOB       (IOC_OFF_PAYLOAD + 24u)
/* ep2drv[1][OUT].  If the bind wrote here instead of [IN], tu_edpt_dir()
 * returned the wrong direction and the map is written to the wrong slot. */
#define IOC_OFF_HIDE_EP2DRVOUT     (IOC_OFF_PAYLOAD + 25u)
#define IOC_HID_ENUM_PAYLOAD_LEN   26u

/* Page 5: the HID class driver's set-config chain.  STATE is the last value
 * process_set_config() was entered with: 0 SET_IDLE, 1 SET_PROTOCOL,
 * 2 GET_REPORT_DESC, 3 COMPLETE, FFh never entered.  ITFNUM and BREQ are read
 * through xfer->setup, a pointer to a caller local -- garbage there sends
 * requests to a nonexistent interface, which a device answers with STALL. */
#define IOC_OFF_HIDC_PAGE          (IOC_OFF_PAYLOAD + 0u)
#define IOC_OFF_HIDC_OPEN          (IOC_OFF_PAYLOAD + 1u)
#define IOC_OFF_HIDC_SETCFG        (IOC_OFF_PAYLOAD + 2u)
#define IOC_OFF_HIDC_PROC          (IOC_OFF_PAYLOAD + 3u)
#define IOC_OFF_HIDC_STATE         (IOC_OFF_PAYLOAD + 4u)
#define IOC_OFF_HIDC_ITFNUM        (IOC_OFF_PAYLOAD + 5u)
#define IOC_OFF_HIDC_BREQ          (IOC_OFF_PAYLOAD + 6u)
#define IOC_OFF_HIDC_RESULT        (IOC_OFF_PAYLOAD + 7u)
#define IOC_OFF_HIDC_MOUNT         (IOC_OFF_PAYLOAD + 8u)
#define IOC_OFF_HIDC_MOUNTCB       (IOC_OFF_PAYLOAD + 9u)
#define IOC_OFF_HIDC_MOUNTS        (IOC_OFF_PAYLOAD + 10u)
#define IOC_OFF_HIDC_DADDR         (IOC_OFF_PAYLOAD + 11u)
#define IOC_OFF_HIDC_INST          (IOC_OFF_PAYLOAD + 12u)
#define IOC_OFF_HIDC_PROTO         (IOC_OFF_PAYLOAD + 13u)
#define IOC_OFF_HIDC_ARM           (IOC_OFF_PAYLOAD + 14u)
#define IOC_OFF_HIDC_KBDSTATE      (IOC_OFF_PAYLOAD + 15u)
#define IOC_OFF_HIDC_KBDPKT        (IOC_OFF_PAYLOAD + 16u)
#define IOC_OFF_HIDC_KBDEP2DRV     (IOC_OFF_PAYLOAD + 17u)
#define IOC_OFF_HIDC_BUSY          (IOC_OFF_PAYLOAD + 18u)
#define IOC_OFF_HIDC_EPIN          (IOC_OFF_PAYLOAD + 19u)
#define IOC_OFF_HIDC_KSUBMIT       (IOC_OFF_PAYLOAD + 20u)
#define IOC_OFF_HIDC_XFERCB        (IOC_OFF_PAYLOAD + 21u)
#define IOC_OFF_HIDC_XFERCBEP      (IOC_OFF_PAYLOAD + 22u)
#define IOC_OFF_HIDC_RPTCB         (IOC_OFF_PAYLOAD + 23u)
#define IOC_OFF_HIDC_RPTDADDR      (IOC_OFF_PAYLOAD + 24u)
#define IOC_OFF_HIDC_RPTINST       (IOC_OFF_PAYLOAD + 25u)
#define IOC_HID_HIDCFG_PAYLOAD_LEN 26u

/* Six 16-bit millisecond totals at bytes 4-15; see timebase.h for the slots. */
#define IOC_OFF_PROFILE_0        (IOC_OFF_PAYLOAD + 0u)
#define IOC_OFF_PROFILE_CALLS    (IOC_OFF_PAYLOAD + 12u)
#define IOC_OFF_PROFILE_ABORTS   (IOC_OFF_PAYLOAD + 14u)
/* SD CMD0 response trace, 8 bytes.  Carried by PROFILE because PING has no
 * spare bytes and this is a bring-up diagnostic, not a hot-path field.
 * See sd_card.h: all FFh = nothing driving DO; all 00h = DO stuck low; mixed
 * junk = the card IS talking and the fault is clocking or alignment; 01h
 * present = CMD0 actually succeeded and the failure is later. */
#define IOC_OFF_PROFILE_SDTRACE  (IOC_OFF_PAYLOAD + 16u)
#define IOC_PROFILE_PAYLOAD_LEN  24u
/* A one-byte PROFILE request with this value asks for a clean measurement
 * interval.  The reset is deferred until the reply has completely left the
 * command lane, so the reset transaction is not counted in the new interval. */
#define IOC_OFF_PROFILE_CONTROL  IOC_OFF_PAYLOAD
#define IOC_OFF_PROFILE_PAGE     (IOC_OFF_PAYLOAD + 1u)
#define IOC_PROFILE_RESET        0x01u
#define IOC_PROFILE_PAGE_SUMMARY 0x00u
#define IOC_PROFILE_PAGE_BULK_TX 0x01u
#define IOC_PROFILE_BULK_TX_LEN  8u

/* STORAGE_PROFILE temporary page, all multibyte fields little endian.
 * Offsets are mailbox offsets; wire payload starts at mailbox byte 4. */
#define IOC_PROFILE_PAGE_SD       0x02u
#define IOC_PROFILE_SD_LEN        16u
#define IOC_PROFILE_SD_VERSION    1u
#define IOC_OFF_SDPROF_VERSION    4u
#define IOC_OFF_SDPROF_FLAGS      5u /* bit 0: recovery/error, timing suspect */
#define IOC_OFF_SDPROF_CALLS      6u /* uint32 */
#define IOC_OFF_SDPROF_TICKS     10u /* uint32, nominal 31 kHz */
#define IOC_OFF_SDPROF_MISSES    14u /* uint16, cumulative wrapping */
#define IOC_OFF_SDPROF_RETRIES   16u /* uint16, cumulative saturating */
#define IOC_OFF_SDPROF_REINITS   18u /* uint16, cumulative saturating */

#define RSP_UNKNOWN_COMMAND  0xFE

/* Firmware capability level, returned by PING.
 *
 * Bump this whenever the frame protocol gains something a host can depend on.
 * It exists because "is the controller running the firmware I just built?" has
 * twice been answered wrongly by inference, and each time cost a debugging
 * round: once when an unflashed build replied RSP_UNKNOWN_COMMAND to a new
 * class, and once when a stale build silently ignored a new request field and
 * returned the same window slice six times.
 *
 *   1  base two-lane transport: PING, SD_READ, BULK_TEST, SD_READ_BULK,
 *      XFER_STATUS, SD_WRITE_BULK
 *   2  frame CRC and rolling sequence
 *   3  bulk-lane CRC in both directions
 *   4  record commands and the SD block cache: SD_READ_REC, SD_WRITE_REC,
 *      SD_FLUSH; XFER_STATUS honours a raw-window offset; the DONE peek
 *      follows the armed receive buffer
 *   5  bulk writes carry a sacrificial lead-in byte before the preamble, and
 *      the receive search widened to 128 bits to keep its late-start margin
 *   6  power handshake: /PWR_OFF driven idle from the first instructions of
 *      startup, /SHUTDOWN_RQ latched and debounced, and both reported by PING
 *  18  common A5/5A LEN16 TYPE SEQ STATUS/DATA CRC16 packet envelope on both
 *      command and bulk lanes; persistent External Sync is unchanged
 *  19  first-transfer sync byte is disposable; a complete A5/5A packet always
 *      follows through SPI, so packet marking is independent of /SYNC timing
 *  20  PROFILE owns Timer3 instead of the command edge counter, and a one-byte
 *      IOC_PROFILE_RESET request starts a clean measurement interval
 *  21  PROFILE page 1 reports bulk-TX wait, preparation, data and teardown
 *      totals; the bulk payload loop streams CRC while SPI2 shifts each byte
 *  22  HID_STATUS reports the MAX3421E bring-up result, revision register and
 *      live /USB_INT pin level without servicing USB or starting enumeration
 *  23  HID_STATUS actively performs visible, read-only MAX3421E revision
 *      bursts at 125 kHz, 1 MHz and 4 MHz and reports all three results
 *  24  MAX3421E is taken out of its power-on half-duplex SPI mode before any
 *      register is read, without which nothing can be read back at all on this
 *      board; HID_STATUS adds a GPOUT write/read-back link test per rate
 *  25  HID_STATUS adds the /USB_INT drive test, which commands the controller
 *      blind and watches its own output pin, separating "cannot hear us" from
 *      "cannot answer us" without relying on MISO
 *  26  revision bursts report a majority verdict and a match count out of 64
 *      rather than the last sample, and the GPOUT result carries a failing-
 *      pattern count, so a marginal link can be graded instead of guessed at
 *  27  USB enumeration is live: /USB_INT is switched to level mode and polled
 *      from the main loop's idle branch, tuh_task() runs, and HID_STATUS
 *      reports mounted devices plus the latest boot keyboard report, and the
 *      mounted device's speed
 *  28  HID_STATUS takes a page selector; page 1 reports raw MAX3421E and stack
 *      state (port connect, MODE/HIRQ/HRSL/USBIRQ, task and dispatch counts)
 *  29  port supplies tusb_time_delay_ms_api() so enumeration delays cannot
 *      complete early on a coarse tick; HID_STATUS page 1 adds the enumerated
 *      address map, which unlike the device count can see the hub
 *  30  HID_STATUS page 1 adds enumeration milestone counters (attach event,
 *      device descriptor, configuration descriptor) to locate where the
 *      enumeration sequence stops
 *  31  HID_STATUS page 1 reports the last enumeration state, the failed-attempt
 *      count, and control transfers refused for lacking a completion callback
 *  32  HID_STATUS page 1 adds host-controller taps: HXFRDN count, xfer-done
 *      count, find_opened_ep() failures, and the last HRSL seen at completion
 *  33  HID_STATUS page 1 adds started-vs-reported transfer counts, packed into
 *      the last payload byte the transport allows
 *  34  HID_STATUS page 2 reports the endpoint state handle_xfer_done() branched
 *      on, and which branch it took
 *  35  XC8 stages TinyUSB events in dedicated storage before queueing, avoiding
 *      static-auto overlay corruption of completion events
 *  36  XC8 preserves the hub interrupt endpoint address across tuh_edpt_open(),
 *      avoiding a second static-auto overlay that changed endpoint 81h to 00h
 *  37  HID_STATUS page 2 traces the hub endpoint from descriptor parsing to
 *      HCD submission and reports the last control SETUP packet
 *  38  XC8 stores the hub interrupt endpoint from the initialized diagnostic
 *      capture and page 2 snapshots the hub state immediately after that store
 *  39  HID_STATUS page 3 traces the retained hub object through open, class
 *      configuration, hub descriptor completion and each port-power callback
 *  60  HID report arming floors an impossible zero packet length and counts
 *      every intentional HID-interface clear to distinguish state loss from
 *      an unobserved close/reinitialization
 *  61  XC8 preserves hidh_open()'s HID-object pointer across the nested
 *      endpoint-open call; HID_STATUS now reports the actual retained ep_in
 *      field rather than the descriptor-side capture
 *  62  boot-keyboard press transitions are translated to terminal bytes and
 *      queued for the nonblocking HID_INPUT command
 *  66  XFER_STATUS reports the Bulk persistent-sync branch decision and live
 *      PIC flag and /SYNCA state for marker-loss diagnosis
 *  67  Z80-to-MCU Bulk releases /CTSA after packet/CRC acceptance; the
 *      command READY gate, not the transport admission line, covers a slow
 *      SD commit
 *  68  SD trace preserves final CMD0/CMD8/CMD55/ACMD41 responses and the
 *      ACMD41 iteration/baud/state snapshot when card initialisation fails
 *  69  normal and diagnostic build profiles.  A NORMAL build no longer serves
 *      CMD_PROFILE, CMD_BULK_TEST, CMD_SD_READ_BULK or CMD_SD_WRITE_BULK --
 *      they are rejected as unknown classes -- and no longer runs the active
 *      MAX3421E probe or the HIDSTATUS detail pages 1-5.  Every reply LAYOUT is
 *      unchanged: the retired fields keep their offsets and read zero, so a
 *      tool decodes the same frame either way.  Level 69 says which of those
 *      fields carry real measurements.  Build with IOC_PROFILE=diagnostic to
 *      get level 69 firmware with the full surface.
 *  70  HID_STATUS page 6 adds passive, production-safe USB/F310 enumeration,
 *      first report-arm, report-count and decoded-latch state.  VID/PID output
 *      storage is persistent so XC8 cannot overlay it across tuh_vid_pid_get().
 *  71  BULK LANE CRC MOVES INTO THE Z80 SIO, BOTH DIRECTIONS.  That hardware
 *      consumes bits in wire order and the wire is LSB-first, so generator and
 *      checker here are reflected (8408h).  Transmit covers the A5/5A marker
 *      and sends its trailer LOW BYTE FIRST, then TWO trailing bytes so the
 *      host's result is valid before it reads RR1.  Receive seeds the lead-in
 *      and both preamble bytes.  A WIRE-FORMAT CHANGE: flash both together.
 *      The command lane is unchanged, software and MSB-first on both ends.
 *  72  CMD_SD_READ_BLOCK (0Fh): one 512-byte block, addressed by
 *      VOLUME-RELATIVE logical block, mapped through the same volume layer and
 *      served from the same cache as CMD_SD_READ_REC.  It exists so the host
 *      BIOS can deblock: CP/M's record is 128 bytes and the card's block is
 *      512, so a sequential read was paying a whole IOCALL + READY + IOCBULK
 *      per quarter-block.  Deliberately NOT the raw-LBA CMD_SD_READ_BULK,
 *      which is diagnostic-only and bypasses volume mapping.
 *      Additive: a host that never sends 0Fh sees no change.
 */
/* 73: STORAGE_PROFILE diagnostic page 2; no transport format change.
 * 74: FS2 namespace commands 41h-44h (UNLINK/RENAME/MKDIR/RMDIR).  Additive,
 *     but the level MUST move with them: the writable commands 3Dh-40h were
 *     added without bumping it, so old and new firmware were indistinguishable
 *     and a controller that silently drops an unadmitted frame looked exactly
 *     like a host-side hang. */
#define IOC_FW_LEVEL  74

/* PING reply: a snapshot of the power handshake pins.
 *
 * Diagnostic, and the cheapest way to answer the question that keeps coming up:
 * is the controller driving /PWR_OFF, and is the PMU asking for anything? Both
 * ends of that handshake are invisible from the host otherwise, and guessing
 * between "the controller is not running" and "something on the card holds the
 * net low" has already cost several rounds.
 *
 *   bit 0  /PWR_OFF pin level      (PORTF6) 1 = keep power on
 *   bit 1  /PWR_OFF drive level    (LATF6)  what we are asking for
 *   bit 2  /PWR_OFF is an output   (TRIS=0) 1 = we own the pin
 *   bit 3  /SHUTDOWN_RQ pin level  (PORTF7) 0 = the PMU is asking
 *   bit 4  /SHUTDOWN_RQ edge latch (INT2IF) 1 = a falling edge was seen
 *   bit 5  /SHUTDOWN_RQ pull-up on (WPUF7)
 *
 * Bits 0 and 1 disagreeing is the interesting case: it means the pin is being
 * driven to one level and sitting at the other, which is a short or a pull
 * stronger than the driver rather than anything in firmware.
 */
#define IOC_OFF_PING_POWER  21u
#define IOC_PING_PWR_OFF_PIN    0x01u
#define IOC_PING_PWR_OFF_LAT    0x02u
#define IOC_PING_PWR_OFF_DRIVEN 0x04u
#define IOC_PING_SHUTDOWN_PIN   0x08u
#define IOC_PING_SHUTDOWN_LATCH 0x10u
#define IOC_PING_SHUTDOWN_WPU   0x20u
#define IOC_PING_LINK_SYNCED    0x40u
/* The last reset was a PIC18 hardware call-stack overflow or underflow.
 *
 * STVREN is ON, so an overflow resets the device rather than corrupting a
 * return address -- and because the controller drives the host reset pair, a
 * PIC that resets on the same code path every time presents as a machine that
 * reboots continuously with nothing on the console to say why.
 *
 * Latched from PCON0 at startup and cleared there, so this reports the reset
 * that produced the CURRENT session.  Without it the cause has to be inferred
 * from symptoms, which is how an afternoon goes missing. */
#define IOC_PING_STACK_RESET    0x80u

/* PING reply diagnostics.  PING echoes request DATA bytes 4..19, then appends
 * fields at 20..29 and declares the full 26-byte command DATA length. */
/* Service-loop counters, little-endian.
 *
 * These were in the PROFILE reply, which is a SECOND transaction issued right
 * after PING -- and on an intermittent link the second transaction is precisely
 * the one that fails, so the most useful counter was behind the least reliable
 * path.  They displace the SD retry/re-init counters, which have measured zero
 * on every run since they were added.
 *
 * calls  = every entry to service_command_request()
 * aborts = those that gave up before dispatching, i.e. the request did not
 *          decode.  The gap between them is requests thrown away. */
#define IOC_OFF_PING_CALLS_LO   22u
#define IOC_OFF_PING_CALLS_HI   23u
#define IOC_OFF_PING_ABORTS_LO  24u
#define IOC_OFF_PING_ABORTS_HI  25u

/* Bytes 26-29: temporary command-lane source-clock diagnostics.
 *
 * The PIC routes RB3/SCK back into Timer1 and counts rising edges at the PIC
 * pin, not calls to sio_link_exchange().  That includes any PPS/SPI transition
 * the source arithmetic cannot see.  It does not see a transition created
 * downstream by enabling or disabling a 74AHCT125 gate; matching RB3's idle
 * level to the gated clock's pull-up prevents those transitions.  A PING
 * handler runs after its request window but before its reply, so it reports:
 *
 *   RX edges  current request window, expected 36 * 8 = 288 (0120h)
 *   TX edges  preceding steady-state full PING reply plus its trailer,
 *             expected 36 * 8 = 288 (0120h)
 *
 * The first establishing PING reply also has two setup clocks and one
 * disposable sync byte, so it measures 298 (012Ah).  A shorter preceding
 * response legitimately reports fewer.
 *
 * This temporarily displaces the record-read/cache-miss counters. */
#define IOC_OFF_PING_RX_EDGES_LO 26u
#define IOC_OFF_PING_RX_EDGES_HI 27u
#define IOC_OFF_PING_TX_EDGES_LO 28u
#define IOC_OFF_PING_TX_EDGES_HI 29u

/* Legacy names kept so older host tools still assemble; these offsets now
 * carry the edge counters documented above. */
#define IOC_OFF_PING_RECREAD_LO 26u
#define IOC_OFF_PING_RECREAD_HI 27u
#define IOC_OFF_PING_MISS_LO    28u
#define IOC_OFF_PING_MISS_HI    29u

#define IOC_OFF_PING_LEVEL  20u

/* Status bytes */
#define IOC_STATUS_OK            0x00
#define IOC_STATUS_ERROR         0x01
#define IOC_STATUS_UNKNOWN_CMD   0x02

/* SD_READ failures.  These map one-to-one onto SdStatus so a host-side dump of
 * the status byte says which stage of the card bring-up gave up. */
#define IOC_STATUS_SD_NO_RESPONSE 0x10
#define IOC_STATUS_SD_UNUSABLE    0x11
#define IOC_STATUS_SD_NOT_READY   0x12
#define IOC_STATUS_SD_READ_FAIL   0x13
#define IOC_STATUS_SD_BUS         0x14
#define IOC_STATUS_SD_NO_CARD     0x15
#define IOC_STATUS_SD_NO_TOKEN    0x16
#define IOC_STATUS_SD_CRC         0x17
#define IOC_STATUS_SD_WRITE_FAIL  0x18
#define IOC_STATUS_SD_WRITE_REJ   0x19
#define IOC_STATUS_SD_WRITE_BUSY  0x1A

/* Bulk lane failure, reported by DONE. */
#define IOC_STATUS_BULK_FAIL      0x20
#define IOC_STATUS_BULK_NO_HOST   0x21
/* Window was clocked but the alignment preamble never appeared: the host did
 * not transmit, or started outside the search range.  Host-side, not link. */
#define IOC_STATUS_BULK_NO_SYNC   0x22
/* Payload arrived and was de-shifted, but its CRC-16 did not match.  The bulk
 * lane carries no other integrity check, so without this a corrupted block is
 * committed to the card looking exactly like a good one. */
#define IOC_STATUS_BULK_CRC       0x23

/* Volume and filesystem failures.
 *
 * Kept distinct from the SD codes on purpose: "the card did not answer" and
 * "the card is fine but that file is not there" are different problems with
 * different remedies, and collapsing them into IOC_STATUS_ERROR is what makes
 * a storage fault take an afternoon to diagnose. */
#define IOC_STATUS_VOL_UNMOUNTED  0x30  /* no volume on that unit */
#define IOC_STATUS_VOL_RANGE      0x31  /* record past the end of the volume */
#define IOC_STATUS_VOL_BAD_IMAGE  0x32  /* wrong size, or too fragmented */
#define IOC_STATUS_FS_NOT_MOUNTED 0x33  /* card carries no FAT filesystem */
#define IOC_STATUS_FS_NO_FILE     0x34
#define IOC_STATUS_FS_BAD_NAME    0x35  /* separator, traversal, or empty */
#define IOC_STATUS_FS_NO_HANDLE   0x36  /* no file open, or wrong handle */
#define IOC_STATUS_FS_RANGE       0x37  /* chunk longer than IOC_FS_CHUNK_MAX */
#define IOC_STATUS_FS_ERROR       0x38  /* anything else FatFs reported */

/* FS2 status namespace.  Keep semantically different outcomes distinct so
 * the bank-7 compatibility layer can map them to characterized ZSDOS results
 * without guessing.  IOC_STATUS_FS2_TRANSPORT is reserved for a host-side
 * synthesized result; firmware does not claim to diagnose its own lost reply.
 */
#define IOC_STATUS_FS2_NOT_FOUND       0x40
#define IOC_STATUS_FS2_END             0x41
#define IOC_STATUS_FS2_EXISTS          0x42
#define IOC_STATUS_FS2_BAD_NAME        0x43
#define IOC_STATUS_FS2_READ_ONLY       0x44
#define IOC_STATUS_FS2_NO_SPACE        0x45
#define IOC_STATUS_FS2_NOT_DIR         0x46
#define IOC_STATUS_FS2_IS_DIR          0x47
#define IOC_STATUS_FS2_NO_HANDLE       0x48
#define IOC_STATUS_FS2_STALE           0x49
#define IOC_STATUS_FS2_RANGE           0x4A
#define IOC_STATUS_FS2_NO_MEDIA        0x4B
#define IOC_STATUS_FS2_TRANSPORT       0x4C
#define IOC_STATUS_FS2_UNKNOWN_WRITE   0x4D
#define IOC_STATUS_FS2_IO              0x4E

typedef struct {
    uint8_t bytes[IOC_FRAME_SIZE];
} IocFrame;

/* Card status to wire status.  Defined in ioc_status.c; declared here because
 * it is protocol knowledge, and because three layers now need it. */
uint8_t ioc_status_from_sd(SdStatus st);

#endif /* IOC_FRAME_H */
