dumaiss/Zephyr-80/Code/MCU/IOController/src/bulk_channel.c

#include <xc.h>
#include <stdint.h>
#include <stdbool.h>
#include "config.h"
#include "external_sync.h"
#include "sio_link.h"
#include "ioc_frame.h"
#include "bulk_channel.h"
#include "timebase.h"

/* ---------------------------------------------------------------------------
 * Bulk lane on SIO1/A
 * ---------------------------------------------------------------------------
 *
 * Electrically this is the same SPI2 module and the same RB1/RB3 pins as the
 * command lane; only the select and the External Sync strobe differ:
 *
 *      command lane   /SIOB_CS (RA4)   /SYNCB (RA7)
 *      bulk lane      /SIOA_CS (RA5)   /SYNCA (RA6)
 *
 * The establishing byte sequence mirrors external_sync_send(): two setup
 * clocks, one hand-clocked byte carrying the /SYNC edge, then the remainder
 * through SPI2 and a trailing flush byte.  Later transfers use SPI2 for every
 * data byte.  The hand-clocked byte is shared with the command lane as
 * sio_link_clock_sync_byte(); the only alignment difference is
 * BULK_SYNC_DROP_BIT below.
 *
 * A disposable byte carries the one-time sync edge.  The complete packet then
 * starts with aligned SPI bytes A5 5A, which the host scans before accepting
 * its declared DATA bytes.
 * --------------------------------------------------------------------------- */

/* ---------------------------------------------------------------------------
 * Bulk lane handshake
 * ---------------------------------------------------------------------------
 *
 * Three signals, all on the SIO1/A modem-control pins:
 *
 *   RF1  /SIO1A_INT   in   the host's RTS: "I am in my read loop, go"
 *   RB4  /DCDA        out  software RX-admission level.  The host polls it
 *                          after asserting RTS and before reading a byte.
 *   RB0  /CTSA        out  asserted for the duration of the bulk phase.  The
 *                          host polls it before transmitting and watches it
 *                          deassert for completion.
 *
 * Waiting for RTS replaces the fixed start guard this lane used to need.  The
 * guard was the single largest cost in a sector transfer and it was a guess;
 * this is deterministic. */
#define BULK_HOST_READY_TIMEOUT_MS     500u
#define BULK_PROFILE_TICKS_PER_MS      31u
#define BULK_HOST_READY_TIMEOUT_TICKS  \
    (BULK_HOST_READY_TIMEOUT_MS * BULK_PROFILE_TICKS_PER_MS)

/* After advertising admission, give the host enough time to observe the RR0
 * level and enter its byte loop before opening SIO1/A's clock gate. */
#define BULK_ADMISSION_GUARD_US     100u

/* ---------------------------------------------------------------------------
 * Bulk byte pacing
 *
 * The bulk lane must NOT inherit EXTSYNC_TARGET_BYTE_US.  That constant is
 * sized for the BIOS command-lane receive path, sio_command_get_byte, which
 * costs 151 T-states per byte because of its per-byte call/ret, push/pop and
 * 24-bit timeout reload.
 *
 * The bulk lane is read by an inlined loop in the host program instead:
 *
 *   ld de,#0 / in / and / jr / in / ld (hl),a / inc hl / dec bc / ld a,b /
 *   or c / jr
 *      10  +  11 +  7  + 12 + 11 +     7     +   6    +   6    +   4   +
 *       4  + 12   =  90 T  =  9.0 us at 10 MHz
 *
 * So 16 us per byte was throttling this lane to nearly half its capacity for no
 * reason.  10 us leaves ~11% margin over the measured host loop, slightly more
 * than the command lane runs with.  Raise to 12 us if a long ISR ever lands
 * inside a transfer; overrun shows up as a corrupt frame, not a clean error.
 * --------------------------------------------------------------------------- */
/* ---------------------------------------------------------------------------
 * Reflected CRC for the bulk lane, both directions
 * ---------------------------------------------------------------------------
 *
 * The Z80's SIO computes this lane's CRC in hardware now, so what this end
 * computes has to be what that hardware computes.
 *
 * The wire is LSB-first (SPI2CON0bits.LSBF = 1, because the Z80 SIO shifts bit
 * 0 first).  The SIO's CRC logic consumes bits in wire order, so it sees b0..b7
 * of each byte; sio_link_crc16_update walks bytes MSB-first.  Over the same
 * data those differ -- measured 5B9Ch against A205h.  Feeding wire-order bits
 * through the SIO's left-shifting 1021h register is exactly a reflected CRC
 * with polynomial 8408h over the plain bytes, which is this table.
 *
 * BULK LANE ONLY.  sio_link_crc16_update stays MSB-first for the command lane,
 * which is software on both ends and unchanged.
 */
#if !IOC_BULK_CRC_BYPASS
static const uint16_t bulk_crc_table[256] = {
    0x0000u, 0x1189u, 0x2312u, 0x329Bu, 0x4624u, 0x57ADu, 0x6536u, 0x74BFu,
    0x8C48u, 0x9DC1u, 0xAF5Au, 0xBED3u, 0xCA6Cu, 0xDBE5u, 0xE97Eu, 0xF8F7u,
    0x1081u, 0x0108u, 0x3393u, 0x221Au, 0x56A5u, 0x472Cu, 0x75B7u, 0x643Eu,
    0x9CC9u, 0x8D40u, 0xBFDBu, 0xAE52u, 0xDAEDu, 0xCB64u, 0xF9FFu, 0xE876u,
    0x2102u, 0x308Bu, 0x0210u, 0x1399u, 0x6726u, 0x76AFu, 0x4434u, 0x55BDu,
    0xAD4Au, 0xBCC3u, 0x8E58u, 0x9FD1u, 0xEB6Eu, 0xFAE7u, 0xC87Cu, 0xD9F5u,
    0x3183u, 0x200Au, 0x1291u, 0x0318u, 0x77A7u, 0x662Eu, 0x54B5u, 0x453Cu,
    0xBDCBu, 0xAC42u, 0x9ED9u, 0x8F50u, 0xFBEFu, 0xEA66u, 0xD8FDu, 0xC974u,
    0x4204u, 0x538Du, 0x6116u, 0x709Fu, 0x0420u, 0x15A9u, 0x2732u, 0x36BBu,
    0xCE4Cu, 0xDFC5u, 0xED5Eu, 0xFCD7u, 0x8868u, 0x99E1u, 0xAB7Au, 0xBAF3u,
    0x5285u, 0x430Cu, 0x7197u, 0x601Eu, 0x14A1u, 0x0528u, 0x37B3u, 0x263Au,
    0xDECDu, 0xCF44u, 0xFDDFu, 0xEC56u, 0x98E9u, 0x8960u, 0xBBFBu, 0xAA72u,
    0x6306u, 0x728Fu, 0x4014u, 0x519Du, 0x2522u, 0x34ABu, 0x0630u, 0x17B9u,
    0xEF4Eu, 0xFEC7u, 0xCC5Cu, 0xDDD5u, 0xA96Au, 0xB8E3u, 0x8A78u, 0x9BF1u,
    0x7387u, 0x620Eu, 0x5095u, 0x411Cu, 0x35A3u, 0x242Au, 0x16B1u, 0x0738u,
    0xFFCFu, 0xEE46u, 0xDCDDu, 0xCD54u, 0xB9EBu, 0xA862u, 0x9AF9u, 0x8B70u,
    0x8408u, 0x9581u, 0xA71Au, 0xB693u, 0xC22Cu, 0xD3A5u, 0xE13Eu, 0xF0B7u,
    0x0840u, 0x19C9u, 0x2B52u, 0x3ADBu, 0x4E64u, 0x5FEDu, 0x6D76u, 0x7CFFu,
    0x9489u, 0x8500u, 0xB79Bu, 0xA612u, 0xD2ADu, 0xC324u, 0xF1BFu, 0xE036u,
    0x18C1u, 0x0948u, 0x3BD3u, 0x2A5Au, 0x5EE5u, 0x4F6Cu, 0x7DF7u, 0x6C7Eu,
    0xA50Au, 0xB483u, 0x8618u, 0x9791u, 0xE32Eu, 0xF2A7u, 0xC03Cu, 0xD1B5u,
    0x2942u, 0x38CBu, 0x0A50u, 0x1BD9u, 0x6F66u, 0x7EEFu, 0x4C74u, 0x5DFDu,
    0xB58Bu, 0xA402u, 0x9699u, 0x8710u, 0xF3AFu, 0xE226u, 0xD0BDu, 0xC134u,
    0x39C3u, 0x284Au, 0x1AD1u, 0x0B58u, 0x7FE7u, 0x6E6Eu, 0x5CF5u, 0x4D7Cu,
    0xC60Cu, 0xD785u, 0xE51Eu, 0xF497u, 0x8028u, 0x91A1u, 0xA33Au, 0xB2B3u,
    0x4A44u, 0x5BCDu, 0x6956u, 0x78DFu, 0x0C60u, 0x1DE9u, 0x2F72u, 0x3EFBu,
    0xD68Du, 0xC704u, 0xF59Fu, 0xE416u, 0x90A9u, 0x8120u, 0xB3BBu, 0xA232u,
    0x5AC5u, 0x4B4Cu, 0x79D7u, 0x685Eu, 0x1CE1u, 0x0D68u, 0x3FF3u, 0x2E7Au,
    0xE70Eu, 0xF687u, 0xC41Cu, 0xD595u, 0xA12Au, 0xB0A3u, 0x8238u, 0x93B1u,
    0x6B46u, 0x7ACFu, 0x4854u, 0x59DDu, 0x2D62u, 0x3CEBu, 0x0E70u, 0x1FF9u,
    0xF78Fu, 0xE606u, 0xD49Du, 0xC514u, 0xB1ABu, 0xA022u, 0x92B9u, 0x8330u,
    0x7BC7u, 0x6A4Eu, 0x58D5u, 0x495Cu, 0x3DE3u, 0x2C6Au, 0x1EF1u, 0x0F78u,
};

static uint16_t bulk_crc_update(uint16_t crc, uint8_t data)
{
    return (uint16_t)((crc >> 8) ^ bulk_crc_table[(uint8_t)((crc ^ data) & 0xFFu)]);
}
#endif

/* The bulk lane runs SPI2 faster than the command lane.  SCK = 64 MHz /
 * (2 * (BAUD+1)), so BAUD 15 gives 2 MHz and 4 us of clocking per byte, against
 * BAUD 31 / 1 MHz / 8 us on the command lane.
 *
 * 6 us per byte is then PIC-bound: 4 us of clocking plus roughly 2 us of loop
 * overhead per byte.  The host's INI-based read loop costs 56 T-states = 5.6 us
 * at 10 MHz, so the host keeps up with margin to spare.  The SIO itself is good
 * for about 3.2 us/byte at a 10 MHz clock, so it is not the constraint either.
 *
 * The direct payload loop below overlaps CRC work with those four wire
 * microseconds.  The zero-gap version proved too fast for the host: the first
 * transfer timed out before a complete header was captured.  Keep a one-us
 * payload guard here; fixed packet bytes retain the full two-us gap because
 * they do not perform overlapping CRC work.  DMA is only relevant if a later
 * design tries to go below the host-safe byte period. */
#define BULK_SPI_BAUD         15u   /* 64 MHz / (2 * 16) = 2 MHz */
#define BULK_SPI_BYTE_US      ((8u * 2u * (BULK_SPI_BAUD + 1u)) / 64u)
#define BULK_TARGET_BYTE_US   6u
#define BULK_BYTE_GAP_US      (BULK_TARGET_BYTE_US - BULK_SPI_BYTE_US)
#define BULK_PAYLOAD_GAP_US   1u

/* The direct payload loop uses an 8-bit guard instead of rebuilding the
 * generic exchange routine's 16-bit, slowest-baud timeout for every byte.
 * At 16 MIPS this still allows many times the expected 4 us SPI transfer. */
#define BULK_SPI_TIMEOUT_POLLS 255u

#if (BULK_TARGET_BYTE_US <= BULK_SPI_BYTE_US)
#error "BULK_TARGET_BYTE_US must exceed the SPI clocking time per byte"
#endif

/* Capture window for a Z80 -> MCU transfer.
 *
 * Room for the payload, the two-byte preamble, and enough slack that the
 * preamble can still be found if the host's transmitter starts late.  The
 * search covers BULK_RX_SEARCH_BITS bit positions, so the window needs that
 * many bits of headroom plus one byte for the bit-shifted tail read. */
/* Widened from 64.  The host now sends a sacrificial lead-in byte before the
 * marker, because the first byte out of its transmitter is fill rather than
 * what was buffered, so A5 5A starts a byte later than it used to.  64 bits
 * would still cover that, but the margin for a late start is what absorbs this
 * class of fault and it should not be spent on a known, fixed cost.
 *
 * A wider search means more candidate positions and so more chances of a false
 * lock on 16 payload bits that happen to read A5 5A.  That is survivable only
 * because the whole packet carries a CRC: a false lock de-shifts into
 * garbage and is rejected rather than committed. */
#define BULK_RX_SEARCH_BITS   128u
#define BULK_PACKET_OVERHEAD  (2u + 2u + IOC_PACKET_FIXED_LEN + IOC_PACKET_CRC_BYTES)
#define BULK_RX_WINDOW_BYTES  (BULK_MAX_LENGTH + BULK_PACKET_OVERHEAD + \
                               (BULK_RX_SEARCH_BITS / 8u) + 2u)

static uint8_t rx_window[BULK_RX_WINDOW_BYTES];

/* Reassemble one LSB-first byte starting at an arbitrary bit position. */
static uint8_t rx_wire_byte(uint16_t bit_index)
{
    uint8_t  i;
    uint8_t  value = 0u;
    uint16_t b;

    for (i = 0u; i < 8u; i++) {
        b = (uint16_t)(bit_index + i);
        if ((rx_window[b >> 3] >> (b & 7u)) & 1u)
            value |= (uint8_t)(1u << i);
    }

    return value;
}

/* Locate the payload by finding the two-byte preamble.  Returns the bit index
 * of the first payload byte. */
static bool find_bulk_start(uint16_t *bit_index)
{
    uint16_t start;

    for (start = 0u; start < BULK_RX_SEARCH_BITS; start++) {
        if (rx_wire_byte(start) != BULK_RX_PREAMBLE_0)
            continue;
        if (rx_wire_byte((uint16_t)(start + 8u)) != BULK_RX_PREAMBLE_1)
            continue;
        *bit_index = (uint16_t)(start + 16u);
        return true;
    }

    return false;
}

/* Pace the bulk lane to what the host's inlined read loop can drain. */
static void bulk_byte_gap(void)
{
    __delay_us(BULK_BYTE_GAP_US);
}

static bool bulk_send_packet_byte(uint8_t value)
{
    uint8_t discard;

    if (!sio_link_exchange(value, &discard))
        return false;
    bulk_byte_gap();
    return true;
}

/* ---------------------------------------------------------------------------
 * Receive pacing (Z80 -> MCU) is NOT the send figure, and is deliberately
 * slacker.
 *
 * BULK_TARGET_BYTE_US is sized against the host's INI read loop, where being
 * slightly too fast costs nothing: the host simply has not seen the byte yet
 * and polls again.
 *
 * Receiving inverts the risk.  The MCU supplies the clock, so if it clocks
 * faster than the host's transmit loop can refill the SIO, the transmitter
 * under-runs and streams its WR7 fill character.  On this channel WR7 is 00h,
 * so the MCU captures a perfectly well-formed block of zeros, the preamble
 * search still succeeds, and the block is committed to the card.  The failure
 * is SILENT and looks exactly like a successful write of zeros.
 *
 * Worse, once the Tx Underrun latch sets the transmitter stops consuming the
 * buffer, so the host's TBE never re-asserts and it times out -- which is how
 * this was found.
 *
 * The host's OUTI-based transmit loop costs 56 T-states = 5.6 us at 10 MHz,
 * the same as its INI read loop.  12 us is a bit over 2x that.  The extra
 * margin is cheap -- 512 bytes takes 6.1 ms instead of 3.1 ms -- and buys
 * protection against a failure mode that corrupts data without reporting it.
 * Do not tune this down to match the send direction; they are not symmetric.
 * --------------------------------------------------------------------------- */
/* 24 us, not 12.
 *
 * The host's OUTI loop costs 5.6 us/byte, so 12 us left it 6.4 us of slack --
 * less than one interrupt.  A CTC ISR measured at 117 T-states (98 T of handler
 * plus 19 T of IM2 acknowledge) is 11.7 us at 10 MHz, so a single interrupt
 * landing inside a transfer put the host further behind than one byte's slack,
 * and with only about two byte-times of buffering in the SIO's transmit path
 * the transmitter ran dry.  Under CTC load at 1 ms that failed ~65% of writes.
 *
 * At 24 us the slack is 18.4 us per byte, comfortably more than one ISR, so a
 * single interrupt is absorbed within the byte it lands in.
 *
 * The cost is 12.4 ms per 512-byte block instead of 6.2 ms -- about 41 kB/s.
 * That is ample for CP/M storage, where SD command latency dominates anyway,
 * and it buys tolerance of the interrupt load that real console traffic will
 * produce.  Reads are unaffected: their 3-byte RX FIFO already absorbs ~18 us
 * and they ran clean under the same load. */
#define BULK_RX_TARGET_BYTE_US  24u
#define BULK_RX_BYTE_GAP_US     (BULK_RX_TARGET_BYTE_US - BULK_SPI_BYTE_US)

#if (BULK_RX_TARGET_BYTE_US <= BULK_SPI_BYTE_US)
#error "BULK_RX_TARGET_BYTE_US must exceed the SPI clocking time per byte"
#endif

static void bulk_rx_byte_gap(void)
{
    __delay_us(BULK_RX_BYTE_GAP_US);
}

static const uint8_t *armed_buf;
static uint8_t       *armed_rx_buf;

/* Survives teardown: armed_rx_buf is cleared before the payload is de-shifted,
 * but a diagnostic issued after the transfer still needs to know where the
 * bytes went. */
static uint8_t *last_rx_target;
static BulkCommitFn   armed_commit;
static uint8_t        armed_dir;
static uint16_t       armed_length;
static uint8_t        armed_xfer_id;
static uint8_t        armed_type;
static uint8_t        armed_sequence;
static uint8_t        armed_status;
static uint8_t        xfer_id_counter;
static uint8_t        last_xfer_id;
static uint8_t        last_status;

/* Bounded wait for the host's RTS on channel A.  Bounded so a host that never
 * arrives fails one transfer instead of wedging the controller. */
static bool wait_for_host_ready(void)
{
    uint16_t start = timebase_us_now();

    for (;;) {
        if (SIO1A_INT_PORT == SIO1A_INT_ACTIVE)
            return true;

        /* The request is a persistent level, so there is no reason to sleep
         * for one millisecond between samples.  Timer3 gives the same bounded
         * 500 ms failure contract without adding ~1 ms to every good transfer.
         * Unsigned subtraction remains valid across one Timer3 wrap. */
        if ((uint16_t)(timebase_us_now() - start) >=
            (uint16_t)BULK_HOST_READY_TIMEOUT_TICKS)
            return false;
    }
}

static void sync_a_release(void)
{
    SYNCA_LAT = SYNCA_IDLE;
}

/* Persistent External Sync on this lane, exactly as on the command lane.
 *
 * /SYNCA idles high, is driven low ONCE by the hand-clocked byte below, and is
 * then held there for the life of the link.  Releasing it per transfer -- which
 * this lane did until now -- forces the host back into Hunt every time and makes
 * the bit-banged byte mandatory on every transfer.
 *
 * The two lanes must behave identically apart from block size, so everything
 * here mirrors external_sync.c; only BULK_SYNC_DROP_BIT and the baud differ. */
static uint8_t last_sync_decision;
static bool bulk_synced;
void bulk_channel_request_resync(void)
{
    /* Release the line first, so the next establishing transfer has a HIGH
     * level to produce a real falling edge from. */
    sync_a_release();
    bulk_synced = false;
}

/* Bit position, within the hand-clocked byte, where /SYNCA is driven low.
 *
 * One bit EARLIER than the command lane's EXTSYNC_SYNC_DROP_BIT.  Both lanes
 * now share sio_link_clock_sync_byte(); this constant is the only difference
 * between them.
 *
 * That is measured, not guessed.  With the drop at bit 1 (mirroring channel B)
 * the bulk lane read back 80h where the ramp's first byte is 00h.  The ramp on
 * the wire is LSB-first:
 *
 *     byte 0 = 00 : 0 0 0 0 0 0 0 0
 *     byte 1 = 01 : 1 0 0 0 0 0 0 0
 *
 * A receive window starting one bit late assembles wire positions 1..8 =
 * 0,0,0,0,0,0,0,1, which LSB-first is 80h.  A window one bit early would have
 * produced 00h, indistinguishable from correct -- so the direction is certain.
 * Dropping /SYNC a bit earlier moves the window back into alignment.
 *
 * RULED OUT 2026-08-23: Auto Enables is not the cause.
 *
 * Channel A was run with WR3 = D1h -- Auto Enables off, otherwise byte-identical
 * to the command channel's WR3 -- against a drop at bit 1.  It still came back
 * exactly one bit late.  The bulk ramp read 80h for 00h, and a sector read
 * returned 2A D5 where the boot signature is 55 AA, which is
 * (55h >> 1) and (AAh >> 1) | 80h: a whole-stream one-bit shift, not corruption.
 *
 * The result is clean.  A stuck RTS was the worry going in, since Auto Enables
 * off also stops /CTSA gating the transmitter -- but a stuck RTS would have
 * produced a timeout or no data at all, and instead all 512 bytes arrived
 * correctly framed and merely shifted.
 *
 * Everything reachable from software has now been eliminated:
 *
 *   WR3            byte-identical (tested: D1h on A behaves as F1h does)
 *   WR4            byte-identical, 30h, External Sync, x1 clock (inspection)
 *   setup clocks   identical count and shape (inspection)
 *   bit-bang shape identical; /SYNC drops at the same point within its bit
 *   gate timing    ruled out (tested: see the select in run_if_armed)
 *
 * RxCA and RxCB come from the same PIC pin, each through a '125 gated by its
 * own channel select, and both are pulled up.  /SYNCA and /SYNCB run directly
 * from the PIC, ungated.  Given the pull-ups, gate-open drives RxC high->low
 * (a falling edge, harmless -- the SIO clocks receive data on the rising edge)
 * and gate-close gives low->high, one phantom rising edge after every transfer
 * on BOTH channels.  Symmetric, so it does not explain A against B either.
 *
 * So the difference is in hardware and is not currently explained.  The
 * measurement that would settle it is a rising-edge COUNT at the SIO's RxC pin
 * -- after the '125, so it is what the receiver actually sees -- between /SYNC
 * going low and the end of that byte, taken on each channel.  That count is
 * exactly what sets the window.  Another firmware experiment will not find it.
 *
 * WR7 is the one remaining software asymmetry (7Eh on B, 00h on A) but should
 * be inert in External Sync mode, where the /SYNC pin -- not the sync character
 * registers -- establishes framing. */
#define BULK_SYNC_DROP_BIT  0u

void bulk_channel_arm(const uint8_t *buf, uint16_t length, uint8_t xfer_id,
                      uint8_t type, uint8_t sequence, uint8_t status)
{
    armed_buf     = buf;
    armed_rx_buf  = 0;
    armed_commit  = 0;
    armed_dir     = BULK_DIR_MCU_TO_Z80;
    armed_length  = length;
    armed_xfer_id = xfer_id;
    armed_type    = type;
    armed_sequence = sequence;
    armed_status  = status;
}

void bulk_channel_arm_receive(uint8_t *buf, uint16_t length, uint8_t xfer_id,
                              uint8_t type, uint8_t sequence,
                              BulkCommitFn commit)
{
    armed_buf     = 0;
    armed_rx_buf  = buf;
    last_rx_target = buf;
    armed_commit  = commit;
    armed_dir     = BULK_DIR_Z80_TO_MCU;
    armed_length  = length;
    armed_xfer_id = xfer_id;
    armed_type    = type;
    armed_sequence = sequence;
    armed_status  = IOC_STATUS_OK;
}

const uint8_t *bulk_channel_rx_target(void)
{
    return last_rx_target;
}

uint16_t bulk_channel_rx_window_size(void)
{
    return BULK_RX_WINDOW_BYTES;
}

const uint8_t *bulk_channel_rx_window(void)
{
    return rx_window;
}

uint8_t bulk_channel_last_xfer_id(void)
{
    return last_xfer_id;
}

uint8_t bulk_channel_last_status(void)
{
    return last_status;
}

uint8_t bulk_channel_sync_decision(void)
{
    return last_sync_decision;
}

uint8_t bulk_channel_sync_live(void)
{
    uint8_t value = 0u;

    if (bulk_synced)
        value |= 0x01u;
    if (SYNCA_LAT == SYNCA_ASSERTED)
        value |= 0x02u;
    return value;
}

uint8_t bulk_channel_next_xfer_id(void)
{
    xfer_id_counter++;
    if (xfer_id_counter == 0u)
        xfer_id_counter = 1u;   /* 0 is reserved for "no transfer" */
    return xfer_id_counter;
}

/* MCU -> Z80 common packet.  A5 carries the one-time /SYNCA edge; the host
 * searches A5 5A before accepting LEN/TYPE/SEQ/STATUS/data. */
static bool bulk_run_send(void)
{
    uint16_t packet_length;
    uint16_t crc;
    uint16_t remaining;
    uint16_t t;
    const uint8_t *payload;
    uint8_t  discard;
    uint8_t  guard;
    uint8_t  value;
    bool     ok = true;

    t = timebase_us_now();

    /* Advertise RX admission and mark the bulk phase live.  Auto Enables is
     * off, so these are status levels; they never disable the host receiver. */
    DCDA_LAT = DCDA_ASSERTED;
    CTSA_LAT = CTSA_ASSERTED;
    __delay_us(BULK_ADMISSION_GUARD_US);

    /* Park SCK at the gated clock's pulled-up idle level before selecting.
     * Otherwise enabling the '125 while the PIC drives low creates a falling
     * transition ahead of bit 0; releasing it creates the corresponding extra
     * rising edge that breaks persistent command-lane alignment. */
    SIO_SCK_LAT  = 1;
    SIO_MOSI_LAT = 1;

    /* Select last, immediately before clocking, matching channel B.
     *
     * This used to be asserted before the /DCDA settle, leaving the clock gate
     * open and idle for 100 us.  /SIOA_CS gates RxCA through a '125, so that
     * was a candidate for the one-bit offset against channel B.  Tested
     * 2026-08-23 with BULK_SYNC_DROP_BIT held at 0: both the ramp and a sector
     * read still passed, so gate-open timing does NOT affect where the receive
     * window lands.  Candidate ruled out.
     *
     * The ordering is kept anyway: it is proven on hardware and it removes an
     * asymmetry against the command lane for no cost. */
    SIOA_CS_LAT = SIOA_CS_ASSERTED;

    /* Snapshot the exact branch inputs before touching either one.  This is
     * reported later through XFER_STATUS, after the host has unwound a failed
     * receive, so it adds no command traffic or timing to the Bulk phase. */
    last_sync_decision = 0u;
    if (bulk_synced)
        last_sync_decision |= 0x01u;
    if (SYNCA_LAT == SYNCA_IDLE)
        last_sync_decision |= 0x02u;

    if (!bulk_synced) {
        last_sync_decision |= 0x04u;
        /* Two setup clocks with /SYNCA still idle, as on the command lane.
         * NOT a multiple of eight, so they would move a synchronised receiver's
         * character boundary -- which is why they run only on the path that is
         * establishing that boundary. */
        SIO_SCK_LAT = 0;
        __delay_us(EXTSYNC_BIT_DELAY_US);
        SIO_SCK_LAT = 1;
        __delay_us(EXTSYNC_BIT_DELAY_US);
        SIO_MOSI_LAT = 0;
        SIO_SCK_LAT = 0;
        __delay_us(EXTSYNC_BIT_DELAY_US);
        SIO_SCK_LAT = 1;

        /* Disposable sync byte.  The complete packet marker follows through
         * SPI, independent of the channel-specific /SYNCA drop position. */
        sio_link_clock_sync_byte(EXTSYNC_ESTABLISH_BYTE, SIO_LINK_CH_BULK,
                                 BULK_SYNC_DROP_BIT);
        if (SYNCA_LAT == SYNCA_ASSERTED)
            last_sync_decision |= 0x08u;
        bulk_synced = true;
    }

    packet_length = (uint16_t)(IOC_PACKET_FIXED_LEN + armed_length);

    /* Back to the gated clock's idle level before the module takes the pins. */
    SIO_SCK_LAT = 1;

    sio_link_set_baud(BULK_SPI_BAUD);
    sio_link_clear_fifos();
    sio_link_pins_to_spi();

    uprof_add(UPROF_BULK_PREP, t);
    t = timebase_us_now();

    /* Always send the complete marker as ordinary aligned packet bytes.
     *
     * Marker excluded from the CRC again, matching the software receive.  The host arms its checker while the
     * clock is still gated, before any bit can arrive, so its coverage starts
     * here.  It cannot arm later without the coverage depending on how far
     * behind the wire it happens to be. */
    /* Marker excluded from the CRC, and MSB-first below: THE HOST'S RECEIVE IS
     * BACK ON SOFTWARE.  Only its transmit uses the SIO's hardware, and the two
     * directions are independent -- changing them together is what took B: out
     * twice. */
    ok = bulk_send_packet_byte(IOC_PACKET_SYNC0);
    if (ok) ok = bulk_send_packet_byte(IOC_PACKET_SYNC1);
    crc = 0u;

    /* Header setup
     * is fixed cost; the 512-byte payload below updates CRC while SPI2 is
     * already shifting the same byte, removing the old complete pre-pass. */
#if !IOC_BULK_CRC_BYPASS
    crc = sio_link_crc16_update(crc, (uint8_t)packet_length);
#endif
    if (ok) ok = bulk_send_packet_byte((uint8_t)packet_length);
#if !IOC_BULK_CRC_BYPASS
    crc = sio_link_crc16_update(crc, (uint8_t)(packet_length >> 8));
#endif
    if (ok) ok = bulk_send_packet_byte((uint8_t)(packet_length >> 8));
#if !IOC_BULK_CRC_BYPASS
    crc = sio_link_crc16_update(crc, armed_type);
#endif
    if (ok) ok = bulk_send_packet_byte(armed_type);
#if !IOC_BULK_CRC_BYPASS
    crc = sio_link_crc16_update(crc, armed_sequence);
#endif
    if (ok) ok = bulk_send_packet_byte(armed_sequence);
#if !IOC_BULK_CRC_BYPASS
    crc = sio_link_crc16_update(crc, armed_status);
#endif
    if (ok) ok = bulk_send_packet_byte(armed_status);

    payload = armed_buf;
    remaining = armed_length;
    while (ok && (remaining != 0u)) {
        value = *payload++;

        /* Start the wire first, then spend its four-microsecond shift time on
         * CRC work.  Direct register access avoids two calls, a pointer
         * argument and a 16-bit timeout setup on every payload byte. */
        SPI2TXB = value;
#if !IOC_BULK_CRC_BYPASS
        crc = sio_link_crc16_update(crc, value);
#endif

        guard = BULK_SPI_TIMEOUT_POLLS;
        while (!PIR5bits.SPI2RXIF) {
            if (--guard == 0u) {
                ok = false;
                break;
            }
        }

        if (!ok)
            break;

        /* CRC and loop work overlap the SPI shift, but are not by themselves
         * enough pacing for the 10 MHz host.  Zero gap failed on transfer 0;
         * one us retains half of the optimization without outrunning INI. */
        discard = SPI2RXB;
        __delay_us(BULK_PAYLOAD_GAP_US);
        remaining--;
    }

    /* Bypass sends two zero bytes to preserve the trailer and flush clocks.
     * Otherwise MSB-first and high byte first: THE HOST'S RECEIVE IS STILL SOFTWARE.
     * Only its transmit uses the SIO's hardware.  The two directions are
     * independent and must not be changed together by reflex -- doing exactly
     * that is what took B: out. */
    if (ok) ok = bulk_send_packet_byte((uint8_t)(crc >> 8));
    if (ok) ok = bulk_send_packet_byte((uint8_t)crc);

    /* One flush byte: the software receive needs no settling time. */
    (void)sio_link_exchange(0xFFu, &discard);
    sio_link_pins_to_lat();

    uprof_add(UPROF_BULK_DATA, t);
    t = timebase_us_now();

    /* /SYNCA is NOT released.  Dropped once by the hand-clocked byte above and
     * held for the life of the link, as the SIO manual requires of an External
     * Sync input.  Releasing it here per transfer is what made the bit-banged
     * byte mandatory on every transfer. */
    SIO_MOSI_LAT = 1;

    /* Close software admission after every byte has been clocked.  The host
     * receiver itself remains enabled and retains its character boundary. */
    CTSA_LAT = CTSA_IDLE;
    DCDA_LAT = DCDA_IDLE;

    SIOA_CS_LAT = SIOA_CS_IDLE;

    armed_length = 0u;

    /* DONE state: the bytes are on the wire.  For a read that is the whole
     * story.  The write direction cannot report success here -- see
     * bulk_run_receive(), which defers DONE until the commit has run. */
    last_xfer_id = armed_xfer_id;
    last_status  = ok ? IOC_STATUS_OK : IOC_STATUS_BULK_FAIL;

    uprof_add(UPROF_BULK_DONE, t);

    return ok;
}

/* Z80 -> MCU.  The MCU still supplies every clock edge, but the host owns the
 * byte phase, so the entire common packet is captured raw and de-shifted after
 * its A5/5A marker is found.
 *
 * /CTSA is software TX admission: the host stages its lead-in, asserts RTS,
 * and waits for /CTSA before streaming.  The staged byte still cannot move
 * early because this MCU supplies every clock and keeps /SIOA_CS closed until
 * after admission.  /DCDA stays idle because no receive admission is offered;
 * the host receiver nevertheless stays enabled and may collect harmless FFh
 * full-duplex bytes, which it drains before the next read. */
static bool bulk_run_receive(void)
{
    uint16_t i;
    uint16_t bit_index;
    uint16_t window;
    uint16_t length;
#if !IOC_BULK_CRC_BYPASS
    uint16_t crc;
#endif
    /* Hoisted from the header-parse block so the CRC probe below can see them. */
    uint16_t declared;
    uint8_t  type;
    uint8_t  sequence;
    uint8_t  status;
    bool     ok = true;

    /* Hold the length locally.  armed_length is cleared during teardown below,
     * before the payload is de-shifted, so the copy loop must not read it --
     * doing so silently copies nothing and leaves the destination buffer at
     * whatever it held before, which then gets committed as if it were the
     * received data. */
    length = armed_length;

    /* Complete common packet plus slack for a late-starting transmitter. */
    window = (uint16_t)(length + BULK_PACKET_OVERHEAD +
                        (BULK_RX_SEARCH_BITS / 8u) + 2u);
    if (window > BULK_RX_WINDOW_BYTES)
        window = BULK_RX_WINDOW_BYTES;

    CTSA_LAT = CTSA_ASSERTED;
    __delay_us(BULK_ADMISSION_GUARD_US);

    /* Match the gated clock's pulled-up idle before enabling the buffer. */
    SIO_SCK_LAT = 1;
    SIOA_CS_LAT = SIOA_CS_ASSERTED;

    /* Marking idle on MOSI.  /SYNCA is already low and stays low; no
     * per-window assert, matching
     * external_sync_receive() on the command lane. */
    SIO_MOSI_LAT = 1;

    sio_link_set_baud(BULK_SPI_BAUD);
    sio_link_clear_fifos();
    sio_link_pins_to_spi();
    for (i = 0u; i < window; i++) {
        if (!sio_link_exchange(0xFFu, &rx_window[i])) {
            ok = false;
            break;
        }
        bulk_rx_byte_gap();
    }
    sio_link_pins_to_lat();

    /* No release here either -- see the send path. */
    SIO_MOSI_LAT = 1;

    SIOA_CS_LAT = SIOA_CS_IDLE;

    /* /CTSA deliberately stays ASSERTED past the end of the byte stream, until
     * the commit below has finished.  For a write it means "this transfer is
     * still in progress", and the commit IS part of the transfer -- the card
     * has not been touched yet when the last byte lands.
     *
     * This is not cosmetic.  The command-lane request detector is edge
     * triggered on /SIO1B_INT, and the PIC samples that line only in its main
     * loop -- so it is blind for the whole card write.  A host that releases
     * channel A and immediately issues the DONE query asserts its RTS while
     * the PIC is inside the write; when the PIC returns, the line is already
     * low and there is no edge left to see.  The request is lost and the host
     * times out after ~11 s.
     *
     * Holding /CTSA across the commit gives the host something real to wait
     * on, so by the time it asks for DONE the PIC is back in its loop and has
     * sampled the idle level.  A host that watches /CTSA cannot lose the race;
     * one that does not, still can. */

    armed_length = 0u;
    last_xfer_id = armed_xfer_id;

    if (!ok) {
        last_status = IOC_STATUS_BULK_FAIL;
        CTSA_LAT = CTSA_IDLE;
        return false;
    }

    if (!find_bulk_start(&bit_index)) {
        /* Clocked the window but never saw the preamble: the host either never
         * transmitted or started so late it fell outside the search.  Distinct
         * from a bus failure, and worth its own code -- it points at the host
         * side, not the link. */
        last_status = IOC_STATUS_BULK_NO_SYNC;
        CTSA_LAT = CTSA_IDLE;
        return false;
    }

    /* bit_index names LEN_LO, immediately after A5 5A. */
    {

        declared = rx_wire_byte(bit_index);
        declared |= (uint16_t)rx_wire_byte((uint16_t)(bit_index + 8u)) << 8;
        type = rx_wire_byte((uint16_t)(bit_index + 16u));
        sequence = rx_wire_byte((uint16_t)(bit_index + 24u));
        status = rx_wire_byte((uint16_t)(bit_index + 32u));

        if (declared != (uint16_t)(IOC_PACKET_FIXED_LEN + length) ||
            type != armed_type || sequence != armed_sequence ||
            status != IOC_STATUS_OK) {
            last_status = IOC_STATUS_BULK_NO_SYNC;
            CTSA_LAT = CTSA_IDLE;
            return false;
        }

#if !IOC_BULK_CRC_BYPASS
        /* The host arms its generator before its first byte leaves, so its
         * coverage is the whole transmission: the sacrificial lead-in, both
         * preamble bytes, then header and payload.  The lead-in never arrives
         * -- that is what makes it sacrificial -- but all three are protocol
         * constants, so they are seeded in.
         *
         * The host cannot arm later.  Its transmitter is two deep, its PUT
         * returns when the buffer frees rather than when the wire is done, and
         * RR1's All Sent reads "Sync: always 1", so it cannot tell which byte
         * is shifting.  Arming before byte one is the only coverage both ends
         * can agree on without a race. */
        crc = 0u;
        crc = bulk_crc_update(crc, BULK_RX_LEADIN);
        crc = bulk_crc_update(crc, BULK_RX_PREAMBLE_0);
        crc = bulk_crc_update(crc, BULK_RX_PREAMBLE_1);
        crc = bulk_crc_update(crc, (uint8_t)declared);
        crc = bulk_crc_update(crc, (uint8_t)(declared >> 8));
        crc = bulk_crc_update(crc, type);
        crc = bulk_crc_update(crc, sequence);
        crc = bulk_crc_update(crc, status);
#endif
    }

    bit_index = (uint16_t)(bit_index + 40u);
    for (i = 0u; i < length; i++) {
        armed_rx_buf[i] = rx_wire_byte((uint16_t)(bit_index + (i * 8u)));
#if !IOC_BULK_CRC_BYPASS
        crc = bulk_crc_update(crc, armed_rx_buf[i]);
#endif
    }

#if !IOC_BULK_CRC_BYPASS
    /* Feed the trailer back through in the order it arrived and require a zero
     * residue -- "An error-free block resolves to zero".  That is immune to
     * whichever byte order the SIO's underrun append emits. */
    {
        uint8_t t0 = rx_wire_byte((uint16_t)(bit_index + (length * 8u)));
        uint8_t t1 = rx_wire_byte((uint16_t)(bit_index + ((length + 1u) * 8u)));
        crc = bulk_crc_update(crc, t0);
        crc = bulk_crc_update(crc, t1);
    }

    if (crc != 0u) {
        /* Do NOT commit.  A block that fails here reached the MCU intact
         * enough to be de-shifted but is not the block the host sent, and
         * writing it would be a silent wrong-data write to the card. */
        last_status = IOC_STATUS_BULK_CRC;
        CTSA_LAT = CTSA_IDLE;
        return false;
    }

#endif

    /* The transport phase is complete once the packet and optional CRC are accepted.
     * Release /CTSA before the potentially slow storage commit: the host's
     * next IOCALL polls COMMAND_READY (/DCDB), which remains deasserted until
     * service_command_request() returns after this commit.  Keeping /CTSA low
     * across an SD write made the transport timeout (~0.45 s) race the card's
     * permitted busy time (0.48 s, plus cache-miss/read/init overhead). */
    CTSA_LAT = CTSA_IDLE;

    /* Only now is DONE meaningful.  Bytes arriving says nothing about whether
     * they were stored. */
    last_status = (armed_commit != 0) ? armed_commit() : IOC_STATUS_OK;

    return (last_status == IOC_STATUS_OK);
}

bool bulk_channel_run_if_armed(void)
{
    uint16_t t;

    if (armed_length == 0u)
        return true;

    /* READY has gone out; wait for the host to say it is ready to move bytes.
     * Same signal in both directions: RTS on channel A. */
    t = timebase_us_now();
    if (!wait_for_host_ready()) {
        uprof_add(UPROF_BULK_WAIT, t);
        armed_length = 0u;
        last_xfer_id = armed_xfer_id;
        last_status  = IOC_STATUS_BULK_NO_HOST;
        return false;
    }
    uprof_add(UPROF_BULK_WAIT, t);

    if (armed_dir == BULK_DIR_Z80_TO_MCU)
        return bulk_run_receive();

    return bulk_run_send();
}
