dumaiss/Zephyr-80/Code/MCU/IOController/src/fs2.c

#include <string.h>
#include <limits.h>

#include "fs2.h"
#include "sdfs.h"
#include "bulk_channel.h"
#include "fs_share.h"
#include "ff.h"

#define FS2_PATH_MAX 239u

typedef struct {
    FIL fil;
    uint32_t generation;
    uint32_t position;
    uint8_t cookie;
    bool open;
    bool writable;
} Fs2File;

typedef struct {
    DIR dir;
    uint32_t generation;
    uint8_t cookie;
    bool open;
} Fs2Dir;

static Fs2File files[IOC_FS2_FILE_SLOTS];
static Fs2Dir directory;
#define chunk fs_bulk_chunk
static char resolver[FS2_PATH_MAX + 1u];
static uint8_t resolver_components;
static uint32_t generation;
#if !FF_FS_READONLY
static Fs2File *pending_write_file;
static uint32_t pending_write_offset;
static uint16_t pending_write_length;
#endif

static void reply_init(const IocFrame *request, IocFrame *reply,
                       uint8_t cls, uint8_t status, uint8_t len)
{
    memset(reply->bytes, 0, IOC_FRAME_SIZE);
    reply->bytes[IOC_OFF_CLASS] = cls;
    reply->bytes[IOC_OFF_SEQ] = request->bytes[IOC_OFF_SEQ];
    reply->bytes[IOC_OFF_STATUS] = status;
    reply->bytes[IOC_OFF_LEN] = len;
}

static void put16(uint8_t *p, uint16_t v)
{
    p[0] = (uint8_t)v;
    p[1] = (uint8_t)(v >> 8);
}

static uint16_t get16(const uint8_t *p)
{
    return (uint16_t)p[0] | ((uint16_t)p[1] << 8);
}

static void put32(uint8_t *p, uint32_t v)
{
    p[0] = (uint8_t)v;
    p[1] = (uint8_t)(v >> 8);
    p[2] = (uint8_t)(v >> 16);
    p[3] = (uint8_t)(v >> 24);
}

static uint32_t get32(const uint8_t *p)
{
    return (uint32_t)p[0] | ((uint32_t)p[1] << 8)
         | ((uint32_t)p[2] << 16) | ((uint32_t)p[3] << 24);
}

static void close_contexts(void)
{
    uint8_t i;

    for (i = 0u; i < IOC_FS2_FILE_SLOTS; ++i) {
        if (files[i].open)
            (void)f_close(&files[i].fil);
        files[i].open = false;
        files[i].writable = false;
        files[i].position = 0uL;
    }
    if (directory.open)
        (void)f_closedir(&directory.dir);
    directory.open = false;
}

static void next_generation(void)
{
    ++generation;
    if (generation == 0uL)
        generation = 1uL;
}

void fs2_init(void)
{
    uint8_t i;

    memset(files, 0, sizeof(files));
    memset(&directory, 0, sizeof(directory));
    for (i = 0u; i < IOC_FS2_FILE_SLOTS; ++i)
        files[i].cookie = (uint8_t)(i + 1u);
    directory.cookie = 1u;
    resolver[0] = '/';
    resolver[1] = '\0';
    resolver_components = 0u;
    generation = 1uL;
}

void fs2_media_invalidated(void)
{
    close_contexts();
    next_generation();
    resolver[0] = '/';
    resolver[1] = '\0';
    resolver_components = 0u;
}

static uint8_t map_result(FRESULT fr)
{
    uint8_t status;

    switch (fr) {
    case FR_OK:            status = IOC_STATUS_OK; break;
    case FR_NO_FILE:
    case FR_NO_PATH:       status = IOC_STATUS_FS2_NOT_FOUND; break;
    case FR_EXIST:         status = IOC_STATUS_FS2_EXISTS; break;
    case FR_INVALID_NAME:  status = IOC_STATUS_FS2_BAD_NAME; break;
    case FR_DENIED:
    case FR_WRITE_PROTECTED: status = IOC_STATUS_FS2_READ_ONLY; break;
    case FR_NOT_ENOUGH_CORE:
    case FR_TOO_MANY_OPEN_FILES: status = IOC_STATUS_FS2_NO_HANDLE; break;
    case FR_INVALID_OBJECT: status = IOC_STATUS_FS2_STALE; break;
    case FR_INVALID_PARAMETER: status = IOC_STATUS_FS2_RANGE; break;
    case FR_NOT_READY:
    case FR_NOT_ENABLED:
    case FR_NO_FILESYSTEM: status = IOC_STATUS_FS2_NO_MEDIA; break;
    default:               status = IOC_STATUS_FS2_IO; break;
    }

    /* A live host can outlast card removal or an SD/FatFs failure.  Drop every
     * open context and advance the generation so no old token can be reused
     * after the volume mounts again. */
    if ((fr == FR_DISK_ERR) || (fr == FR_INT_ERR) ||
        (fr == FR_NOT_READY) || (fr == FR_NOT_ENABLED) ||
        (fr == FR_NO_FILESYSTEM))
        sdfs_invalidate();

    return status;
}

static uint8_t need_fs(FATFS **fs)
{
    SdStatus st = sdfs_mount(fs);
    if (st != SD_OK)
        return IOC_STATUS_FS2_NO_MEDIA;
    if (*fs == NULL)
        return IOC_STATUS_FS2_NO_MEDIA;
    return IOC_STATUS_OK;
}

static bool legal_char(uint8_t c)
{
    if ((c < 0x21u) || (c > 0x7eu))
        return false;
    switch (c) {
    case '"': case '*': case '+': case ',': case '/': case ':':
    case ';': case '<': case '=': case '>': case '?': case '[':
    case '\\': case ']': case '|': case '.': case '~':
        return false;
    default:
        return true;
    }
}

static bool unpack_name(char *out, const uint8_t *name)
{
    uint8_t i;
    uint8_t n = 0u;
    bool saw_space = false;

    for (i = 0u; i < 8u; ++i) {
        uint8_t c = name[i] & 0x7fu;
        if (c == ' ') {
            saw_space = true;
            continue;
        }
        if (saw_space || !legal_char(c))
            return false;
        out[n++] = (char)c;
    }
    if (n == 0u)
        return false;

    saw_space = false;
    if (name[8] != ' ') {
        out[n++] = '.';
        for (i = 8u; i < IOC_NAME_LEN; ++i) {
            uint8_t c = name[i] & 0x7fu;
            if (c == ' ') {
                saw_space = true;
                continue;
            }
            if (saw_space || !legal_char(c))
                return false;
            out[n++] = (char)c;
        }
    } else if ((name[9] != ' ') || (name[10] != ' ')) {
        return false;
    }
    out[n] = '\0';
    return true;
}

static bool pack_name(uint8_t *out, const char *name)
{
    uint8_t b = 0u;
    uint8_t e = 8u;
    bool extension = false;
    uint8_t c;

    memset(out, ' ', IOC_NAME_LEN);
    while ((c = (uint8_t)*name++) != 0u) {
        if (c == '.') {
            if (extension || (b == 0u))
                return false;
            extension = true;
            continue;
        }
        if (!legal_char(c))
            return false;
        if ((c >= 'a') && (c <= 'z'))
            c = (uint8_t)(c - ('a' - 'A'));
        if (!extension) {
            if (b >= 8u)
                return false;
            out[b++] = c;
        } else {
            if (e >= IOC_NAME_LEN)
                return false;
            out[e++] = c;
        }
    }
    return (b != 0u) && (!extension || (e != 8u));
}

static bool make_path(char *out, const uint8_t *name, bool append)
{
    char component[13];
    size_t base;
    size_t add;

    if (!unpack_name(component, name))
        return false;
    base = strlen(resolver);
    add = strlen(component);
    if (base + add + ((base == 1u) ? 0u : 1u) > FS2_PATH_MAX)
        return false;
    memcpy(out, resolver, base);
    if (base != 1u)
        out[base++] = '/';
    memcpy(out + base, component, add + 1u);
    if (append) {
        memcpy(resolver, out, base + add + 1u);
        ++resolver_components;
    }
    return true;
}

static uint16_t token_for(uint8_t slot, uint8_t cookie)
{
    return (uint16_t)(slot + 1u) | ((uint16_t)cookie << 8);
}

static Fs2File *file_for(uint16_t token, uint8_t *status)
{
    uint8_t raw = (uint8_t)token;
    uint8_t slot;
    Fs2File *f;

    if ((raw == 0u) || (raw > IOC_FS2_FILE_SLOTS)) {
        *status = IOC_STATUS_FS2_NO_HANDLE;
        return NULL;
    }
    slot = (uint8_t)(raw - 1u);
    f = &files[slot];
    if (f->cookie != (uint8_t)(token >> 8)) {
        *status = IOC_STATUS_FS2_NO_HANDLE;
        return NULL;
    }
    if (f->generation != generation) {
        *status = IOC_STATUS_FS2_STALE;
        return NULL;
    }
    if (!f->open) {
        *status = IOC_STATUS_FS2_NO_HANDLE;
        return NULL;
    }
    *status = IOC_STATUS_OK;
    return f;
}

void handler_fs2_caps(const IocFrame *request, IocFrame *reply)
{
    uint16_t flags = IOC_FS2_CAP_EXPLICIT_OFFSET
                   | IOC_FS2_CAP_COMPONENT_RESOLVER
                   | IOC_FS2_CAP_MEDIA_GENERATION | IOC_FS2_CAP_STAT
                   | IOC_FS2_CAP_SPACE;
#if FF_FS_READONLY
    flags |= IOC_FS2_CAP_READ_ONLY;
#else
    flags |= IOC_FS2_CAP_WRITE | IOC_FS2_CAP_TRUNCATE
           | IOC_FS2_CAP_UNLINK | IOC_FS2_CAP_RENAME
           | IOC_FS2_CAP_MKDIR | IOC_FS2_CAP_RMDIR;
#endif
    reply_init(request, reply, RSP_FS2_CAPS, IOC_STATUS_OK,
               IOC_FS2_CAP_REPLY_LEN);
    reply->bytes[IOC_OFF_FS2_CAP_VERSION] = IOC_FS2_VERSION;
    reply->bytes[IOC_OFF_FS2_CAP_STATUS_VERSION] = IOC_FS2_STATUS_VERSION;
    put16(&reply->bytes[IOC_OFF_FS2_CAP_FLAGS], flags);
    put32(&reply->bytes[IOC_OFF_FS2_CAP_GENERATION], generation);
    put16(&reply->bytes[IOC_OFF_FS2_CAP_CHUNK_MAX], IOC_FS2_CHUNK_MAX);
    reply->bytes[IOC_OFF_FS2_CAP_FILE_SLOTS] = IOC_FS2_FILE_SLOTS;
    reply->bytes[IOC_OFF_FS2_CAP_DIR_SLOTS] = IOC_FS2_DIR_SLOTS;
    reply->bytes[IOC_OFF_FS2_CAP_RESOLVER_MAX] = IOC_FS2_RESOLVER_COMPONENTS;
    reply->bytes[IOC_OFF_FS2_CAP_TOKEN_BYTES] = IOC_FS2_TOKEN_BYTES;
}

void handler_fs2_generation(const IocFrame *request, IocFrame *reply)
{
    reply_init(request, reply, RSP_FS2_GENERATION, IOC_STATUS_OK,
               IOC_FS2_GENERATION_REPLY_LEN);
    put32(&reply->bytes[IOC_OFF_FS2_GENERATION], generation);
}

void handler_fs2_reset(const IocFrame *request, IocFrame *reply)
{
    fs2_media_invalidated();
    reply_init(request, reply, RSP_FS2_RESET, IOC_STATUS_OK,
               IOC_FS2_GENERATION_REPLY_LEN);
    put32(&reply->bytes[IOC_OFF_FS2_GENERATION], generation);
}

void handler_fs2_root(const IocFrame *request, IocFrame *reply)
{
    resolver[0] = '/';
    resolver[1] = '\0';
    resolver_components = 0u;
    reply_init(request, reply, RSP_FS2_ROOT, IOC_STATUS_OK, 0u);
}

void handler_fs2_push(const IocFrame *request, IocFrame *reply)
{
    char path[FS2_PATH_MAX + 1u];
    FILINFO info;
    FATFS *fs;
    uint8_t status = need_fs(&fs);
    FRESULT fr;
    (void)fs;

    if (status == IOC_STATUS_OK) {
        if (resolver_components >= IOC_FS2_RESOLVER_COMPONENTS)
            status = IOC_STATUS_FS2_RANGE;
        else if (!make_path(path, &request->bytes[IOC_OFF_FS2_NAME], false))
            status = IOC_STATUS_FS2_BAD_NAME;
        else {
            fr = f_stat(path, &info);
            status = map_result(fr);
            if ((status == IOC_STATUS_OK) && ((info.fattrib & AM_DIR) == 0u))
                status = IOC_STATUS_FS2_NOT_DIR;
            if (status == IOC_STATUS_OK)
                (void)make_path(path, &request->bytes[IOC_OFF_FS2_NAME], true);
        }
    }
    reply_init(request, reply, RSP_FS2_PUSH, status, 0u);
}

void handler_fs2_open_ro(const IocFrame *request, IocFrame *reply)
{
    char path[FS2_PATH_MAX + 1u];
    FATFS *fs;
    FILINFO info;
    uint8_t status = need_fs(&fs);
    uint8_t i;
    FRESULT fr;
    Fs2File *file = NULL;
    (void)fs;

    if ((status == IOC_STATUS_OK) &&
        !make_path(path, &request->bytes[IOC_OFF_FS2_NAME], false))
        status = IOC_STATUS_FS2_BAD_NAME;
    if (status == IOC_STATUS_OK) {
        fr = f_stat(path, &info);
        status = map_result(fr);
        if ((status == IOC_STATUS_OK) && ((info.fattrib & AM_DIR) != 0u))
            status = IOC_STATUS_FS2_IS_DIR;
    }
    if (status == IOC_STATUS_OK) {
        for (i = 0u; i < IOC_FS2_FILE_SLOTS; ++i) {
            if (!files[i].open) {
                file = &files[i];
                break;
            }
        }
        if (file == NULL)
            status = IOC_STATUS_FS2_NO_HANDLE;
    }
    if (status == IOC_STATUS_OK) {
        fr = f_open(&file->fil, path, FA_READ);
        status = map_result(fr);
    }
    if (status != IOC_STATUS_OK) {
        reply_init(request, reply, RSP_FS2_OPEN_RO, status, 0u);
        return;
    }
    ++file->cookie;
    if (file->cookie == 0u)
        file->cookie = 1u;
    file->open = true;
    file->writable = false;
    file->generation = generation;
    file->position = 0uL;
    reply_init(request, reply, RSP_FS2_OPEN_RO, IOC_STATUS_OK,
               IOC_FS2_OPEN_REPLY_LEN);
    put16(&reply->bytes[IOC_OFF_FS2_OPEN_TOKEN],
          token_for(i, file->cookie));
    put32(&reply->bytes[IOC_OFF_FS2_OPEN_SIZE], (uint32_t)f_size(&file->fil));
    /* FS2 exposes a read-only namespace.  FAT attributes have no portable
     * meaning to its CP/M or native clients and previously corrupted CP/M
     * 8.3 names when translated into filename high bits. */
    reply->bytes[IOC_OFF_FS2_OPEN_ATTR] = 0u;
}

void handler_fs2_read(const IocFrame *request, IocFrame *reply)
{
    uint16_t token = get16(&request->bytes[IOC_OFF_FS2_TOKEN]);
    uint32_t offset = get32(&request->bytes[IOC_OFF_FS2_OFFSET]);
    uint16_t length = get16(&request->bytes[IOC_OFF_FS2_LENGTH]);
    uint8_t status;
    Fs2File *file = file_for(token, &status);
    FRESULT fr;
    UINT got = 0u;

    if ((status == IOC_STATUS_OK) &&
        ((length == 0u) || (length > IOC_FS2_CHUNK_MAX)))
        status = IOC_STATUS_FS2_RANGE;
    if ((status == IOC_STATUS_OK) && (file->position != offset)) {
        fr = f_lseek(&file->fil, (FSIZE_t)offset);
        status = map_result(fr);
        if (status == IOC_STATUS_OK)
            file->position = offset;
    }
    if (status == IOC_STATUS_OK) {
        fr = f_read(&file->fil, chunk, (UINT)length, &got);
        status = map_result(fr);
        if (status == IOC_STATUS_OK)
            file->position = offset + got;
        else
            file->position = 0xffffffffuL;
    }
    if (status != IOC_STATUS_OK) {
        reply_init(request, reply, RSP_FS2_READ, status, 0u);
        return;
    }
    reply_init(request, reply, RSP_FS2_READ, IOC_STATUS_OK,
               IOC_READY_PAYLOAD_LEN);
    if (got != 0u) {
        reply->bytes[IOC_OFF_READY_XFER_ID] = bulk_channel_next_xfer_id();
        reply->bytes[IOC_OFF_READY_DIRECTION] = BULK_DIR_MCU_TO_Z80;
        put16(&reply->bytes[IOC_OFF_READY_LEN_LO], (uint16_t)got);
        put32(&reply->bytes[IOC_OFF_READY_LBA], offset);
        bulk_channel_arm(chunk, (uint16_t)got,
                         reply->bytes[IOC_OFF_READY_XFER_ID], RSP_FS2_READ,
                         request->bytes[IOC_OFF_SEQ], IOC_STATUS_OK);
    }
}

void handler_fs2_close(const IocFrame *request, IocFrame *reply)
{
    uint16_t token = get16(&request->bytes[IOC_OFF_FS2_TOKEN]);
    uint8_t status;
    Fs2File *file = file_for(token, &status);
    if (status == IOC_STATUS_OK) {
        FRESULT fr = f_close(&file->fil);
        file->open = false;
        file->writable = false;
        file->position = 0uL;
        status = map_result(fr);
    }
    reply_init(request, reply, RSP_FS2_CLOSE, status, 0u);
}

void handler_fs2_opendir(const IocFrame *request, IocFrame *reply)
{
    FATFS *fs;
    uint8_t status = need_fs(&fs);
    FRESULT fr;
    (void)fs;
    if ((status == IOC_STATUS_OK) && directory.open)
        status = IOC_STATUS_FS2_NO_HANDLE;
    if (status == IOC_STATUS_OK) {
        fr = f_opendir(&directory.dir, resolver);
        status = map_result(fr);
    }
    if (status != IOC_STATUS_OK) {
        reply_init(request, reply, RSP_FS2_OPENDIR, status, 0u);
        return;
    }
    ++directory.cookie;
    if (directory.cookie == 0u)
        directory.cookie = 1u;
    directory.open = true;
    directory.generation = generation;
    reply_init(request, reply, RSP_FS2_OPENDIR, IOC_STATUS_OK,
               IOC_FS2_DIR_REPLY_LEN);
    put16(&reply->bytes[IOC_OFF_FS2_DIR_TOKEN],
          token_for(0u, directory.cookie));
}

static uint8_t dir_status(uint16_t token)
{
    if (((uint8_t)token != 1u) ||
        ((uint8_t)(token >> 8) != directory.cookie))
        return IOC_STATUS_FS2_NO_HANDLE;
    if (directory.generation != generation)
        return IOC_STATUS_FS2_STALE;
    if (!directory.open)
        return IOC_STATUS_FS2_NO_HANDLE;
    return IOC_STATUS_OK;
}

void handler_fs2_readdir(const IocFrame *request, IocFrame *reply)
{
    uint16_t token = get16(&request->bytes[IOC_OFF_FS2_TOKEN]);
    uint8_t status = dir_status(token);
    FILINFO info;
    FRESULT fr;
    uint8_t packed[IOC_NAME_LEN];

    while (status == IOC_STATUS_OK) {
        fr = f_readdir(&directory.dir, &info);
        status = map_result(fr);
        if (status != IOC_STATUS_OK)
            break;
        if (info.fname[0] == '\0') {
            status = IOC_STATUS_FS2_END;
            break;
        }
        if (pack_name(packed, info.fname))
            break;
    }
    if (status != IOC_STATUS_OK) {
        reply_init(request, reply, RSP_FS2_READDIR, status, 0u);
        return;
    }
    reply_init(request, reply, RSP_FS2_READDIR, IOC_STATUS_OK,
               IOC_FS2_DIRENT_REPLY_LEN);
    memcpy(&reply->bytes[IOC_OFF_FS2_DIRENT_NAME], packed, IOC_NAME_LEN);
    /* Preserve only the structural directory marker.  Clients need it to
     * distinguish traversable components from files; ordinary FAT attributes
     * remain deliberately hidden. */
    reply->bytes[IOC_OFF_FS2_DIRENT_ATTR] = info.fattrib & AM_DIR;
    put32(&reply->bytes[IOC_OFF_FS2_DIRENT_SIZE], (uint32_t)info.fsize);
}

void handler_fs2_closedir(const IocFrame *request, IocFrame *reply)
{
    uint16_t token = get16(&request->bytes[IOC_OFF_FS2_TOKEN]);
    uint8_t status = dir_status(token);
    if (status == IOC_STATUS_OK) {
        status = map_result(f_closedir(&directory.dir));
        directory.open = false;
    }
    reply_init(request, reply, RSP_FS2_CLOSEDIR, status, 0u);
}

void handler_fs2_stat(const IocFrame *request, IocFrame *reply)
{
    char path[FS2_PATH_MAX + 1u];
    FATFS *fs;
    FILINFO info;
    uint8_t status = need_fs(&fs);
    (void)fs;
    if ((status == IOC_STATUS_OK) &&
        !make_path(path, &request->bytes[IOC_OFF_FS2_NAME], false))
        status = IOC_STATUS_FS2_BAD_NAME;
    if (status == IOC_STATUS_OK)
        status = map_result(f_stat(path, &info));
    if (status != IOC_STATUS_OK) {
        reply_init(request, reply, RSP_FS2_STAT, status, 0u);
        return;
    }
    reply_init(request, reply, RSP_FS2_STAT, IOC_STATUS_OK,
               IOC_FS2_STAT_REPLY_LEN);
    put32(&reply->bytes[IOC_OFF_FS2_STAT_SIZE], (uint32_t)info.fsize);
    reply->bytes[IOC_OFF_FS2_STAT_ATTR] = info.fattrib & AM_DIR;
}

static uint32_t byte_count(DWORD clusters, DWORD cluster_bytes)
{
    if ((cluster_bytes != 0uL) &&
        (clusters > (DWORD)(0xffffffffuL / cluster_bytes)))
        return 0xffffffffuL;
    return (uint32_t)(clusters * cluster_bytes);
}

static uint32_t kibibyte_count(DWORD clusters, DWORD cluster_bytes)
{
    uint64_t kibibytes = ((uint64_t)clusters * cluster_bytes) / 1024uL;
    return kibibytes > 0xffffffffuL ? 0xffffffffuL : (uint32_t)kibibytes;
}

void handler_fs2_space(const IocFrame *request, IocFrame *reply)
{
    FATFS *fs;
    DWORD free_clusters = 0uL;
    DWORD cluster_bytes;
    uint8_t status = need_fs(&fs);
    FRESULT fr;
    if (status == IOC_STATUS_OK) {
        fr = f_getfree("/", &free_clusters, &fs);
        status = map_result(fr);
    }
    if (status != IOC_STATUS_OK) {
        reply_init(request, reply, RSP_FS2_SPACE, status, 0u);
        return;
    }
    cluster_bytes = (DWORD)fs->csize * 512uL;
    reply_init(request, reply, RSP_FS2_SPACE, IOC_STATUS_OK,
               IOC_FS2_SPACE_REPLY_LEN);
    put32(&reply->bytes[IOC_OFF_FS2_SPACE_FREE],
          byte_count(free_clusters, cluster_bytes));
    put32(&reply->bytes[IOC_OFF_FS2_SPACE_TOTAL],
          byte_count(fs->n_fatent - 2uL, cluster_bytes));
    put32(&reply->bytes[IOC_OFF_FS2_SPACE_FREE_KIB],
          kibibyte_count(free_clusters, cluster_bytes));
    put32(&reply->bytes[IOC_OFF_FS2_SPACE_TOTAL_KIB],
          kibibyte_count(fs->n_fatent - 2uL, cluster_bytes));
}

void handler_fs2_open_rw(const IocFrame *request, IocFrame *reply)
{
#if FF_FS_READONLY
    reply_init(request, reply, RSP_FS2_OPEN_RW,
               IOC_STATUS_FS2_READ_ONLY, 0u);
#else
    char path[FS2_PATH_MAX + 1u];
    FATFS *fs;
    uint8_t status = need_fs(&fs);
    uint8_t mode = request->bytes[IOC_OFF_FS2_OPEN_MODE];
    uint8_t flags;
    uint8_t i;
    FRESULT fr;
    Fs2File *file = NULL;
    FILINFO info;
    (void)fs;

    if (mode > IOC_FS2_OPEN_CREATE_ALWAYS)
        status = IOC_STATUS_FS2_RANGE;
    if ((status == IOC_STATUS_OK) &&
        !make_path(path, &request->bytes[IOC_OFF_FS2_OPEN_NAME], false))
        status = IOC_STATUS_FS2_BAD_NAME;
    if (status == IOC_STATUS_OK) {
        fr = f_stat(path, &info);
        if (fr == FR_OK) {
            if ((info.fattrib & AM_DIR) != 0u)
                status = IOC_STATUS_FS2_IS_DIR;
            else if (mode == IOC_FS2_OPEN_CREATE_NEW)
                status = IOC_STATUS_FS2_EXISTS;
        } else if (fr == FR_NO_FILE) {
            if (mode == IOC_FS2_OPEN_UPDATE)
                status = IOC_STATUS_FS2_NOT_FOUND;
        } else {
            status = map_result(fr);
        }
    }
    if (status == IOC_STATUS_OK) {
        for (i = 0u; i < IOC_FS2_FILE_SLOTS; ++i) {
            if (!files[i].open) {
                file = &files[i];
                break;
            }
        }
        if (file == NULL)
            status = IOC_STATUS_FS2_NO_HANDLE;
    }
    if (status == IOC_STATUS_OK) {
        flags = FA_READ | FA_WRITE;
        if (mode == IOC_FS2_OPEN_CREATE_NEW)
            flags |= FA_CREATE_NEW;
        else if (mode == IOC_FS2_OPEN_CREATE_ALWAYS)
            flags |= FA_CREATE_ALWAYS;
        fr = f_open(&file->fil, path, flags);
        status = map_result(fr);
    }
    if (status != IOC_STATUS_OK) {
        reply_init(request, reply, RSP_FS2_OPEN_RW, status, 0u);
        return;
    }
    ++file->cookie;
    if (file->cookie == 0u)
        file->cookie = 1u;
    file->open = true;
    file->writable = true;
    file->generation = generation;
    file->position = 0uL;
    reply_init(request, reply, RSP_FS2_OPEN_RW, IOC_STATUS_OK,
               IOC_FS2_OPEN_REPLY_LEN);
    put16(&reply->bytes[IOC_OFF_FS2_OPEN_TOKEN], token_for(i, file->cookie));
    put32(&reply->bytes[IOC_OFF_FS2_OPEN_SIZE], (uint32_t)f_size(&file->fil));
    reply->bytes[IOC_OFF_FS2_OPEN_ATTR] = 0u;
#endif
}

#if !FF_FS_READONLY
static uint8_t commit_fs2_write(void)
{
    FRESULT fr;
    UINT put = 0u;
    uint8_t status;

    if ((pending_write_file == NULL) || !pending_write_file->open ||
        !pending_write_file->writable ||
        (pending_write_file->generation != generation))
        return IOC_STATUS_FS2_STALE;

    if (pending_write_file->position != pending_write_offset) {
        fr = f_lseek(&pending_write_file->fil, (FSIZE_t)pending_write_offset);
        status = map_result(fr);
        if (status != IOC_STATUS_OK)
            return status;
        pending_write_file->position = pending_write_offset;
    }

    fr = f_write(&pending_write_file->fil, chunk,
                 (UINT)pending_write_length, &put);
    status = map_result(fr);
    if (status != IOC_STATUS_OK)
        return status;
    pending_write_file->position = pending_write_offset + put;
    if (put != pending_write_length)
        return IOC_STATUS_FS2_NO_SPACE;
    return IOC_STATUS_OK;
}
#endif

void handler_fs2_write(const IocFrame *request, IocFrame *reply)
{
#if FF_FS_READONLY
    reply_init(request, reply, RSP_FS2_WRITE,
               IOC_STATUS_FS2_READ_ONLY, 0u);
#else
    uint16_t token = get16(&request->bytes[IOC_OFF_FS2_TOKEN]);
    uint32_t offset = get32(&request->bytes[IOC_OFF_FS2_OFFSET]);
    uint16_t length = get16(&request->bytes[IOC_OFF_FS2_LENGTH]);
    uint8_t status;
    Fs2File *file = file_for(token, &status);

    if ((status == IOC_STATUS_OK) && !file->writable)
        status = IOC_STATUS_FS2_READ_ONLY;
    if ((status == IOC_STATUS_OK) &&
        ((length == 0u) || (length > IOC_FS2_CHUNK_MAX)))
        status = IOC_STATUS_FS2_RANGE;
    if (status != IOC_STATUS_OK) {
        reply_init(request, reply, RSP_FS2_WRITE, status, 0u);
        return;
    }

    pending_write_file = file;
    pending_write_offset = offset;
    pending_write_length = length;
    reply_init(request, reply, RSP_FS2_WRITE, IOC_STATUS_OK,
               IOC_READY_PAYLOAD_LEN);
    reply->bytes[IOC_OFF_READY_XFER_ID] = bulk_channel_next_xfer_id();
    reply->bytes[IOC_OFF_READY_DIRECTION] = BULK_DIR_Z80_TO_MCU;
    put16(&reply->bytes[IOC_OFF_READY_LEN_LO], length);
    put32(&reply->bytes[IOC_OFF_READY_LBA], offset);
    bulk_channel_arm_receive(chunk, length,
                             reply->bytes[IOC_OFF_READY_XFER_ID],
                             CMD_FS2_WRITE, request->bytes[IOC_OFF_SEQ],
                             commit_fs2_write);
#endif
}

#if !FF_FS_READONLY
/* FF_FS_LOCK is 0, so FatFs will not stop a caller from unlinking or renaming
 * a file it still has open -- its own documentation says the application must
 * prevent that or the volume gets corrupted.  FS2 file handles are declared
 * opportunistic, and handler_fs_delete does the same thing for /SHARED, so
 * close them all rather than try to work out which one names this path.  A
 * caller that had uncommitted data lost nothing it had not already written. */
static void close_all_files(void)
{
    uint8_t i;
    for (i = 0u; i < IOC_FS2_FILE_SLOTS; ++i) {
        if (files[i].open) {
            (void)f_close(&files[i].fil);
            files[i].open = false;
            files[i].writable = false;
            files[i].position = 0uL;
        }
    }
}

/* UNLINK, MKDIR and RMDIR differ only in the FatFs call and the reply class. */
static void namespace_op(const IocFrame *request, IocFrame *reply,
                         uint8_t cls, uint8_t op)
{
    char path[FS2_PATH_MAX + 1u];
    FATFS *fs;
    uint8_t status = need_fs(&fs);
    (void)fs;

    if ((status == IOC_STATUS_OK) &&
        !make_path(path, &request->bytes[IOC_OFF_FS2_NAME], false))
        status = IOC_STATUS_FS2_BAD_NAME;
    if (status == IOC_STATUS_OK) {
        if (op == CMD_FS2_MKDIR) {
            status = map_result(f_mkdir(path));
        } else {
            close_all_files();
            status = map_result(f_unlink(path));
        }
    }
    reply_init(request, reply, cls, status, 0u);
}
#endif

void handler_fs2_unlink(const IocFrame *request, IocFrame *reply)
{
#if FF_FS_READONLY
    reply_init(request, reply, RSP_FS2_UNLINK,
               IOC_STATUS_FS2_READ_ONLY, 0u);
#else
    namespace_op(request, reply, RSP_FS2_UNLINK, CMD_FS2_UNLINK);
#endif
}

void handler_fs2_mkdir(const IocFrame *request, IocFrame *reply)
{
#if FF_FS_READONLY
    reply_init(request, reply, RSP_FS2_MKDIR,
               IOC_STATUS_FS2_READ_ONLY, 0u);
#else
    namespace_op(request, reply, RSP_FS2_MKDIR, CMD_FS2_MKDIR);
#endif
}

/* f_unlink removes an empty directory too, and reports FR_DENIED when it is
 * not empty; map_result turns that into the read-only/denied status. */
void handler_fs2_rmdir(const IocFrame *request, IocFrame *reply)
{
#if FF_FS_READONLY
    reply_init(request, reply, RSP_FS2_RMDIR,
               IOC_STATUS_FS2_READ_ONLY, 0u);
#else
    namespace_op(request, reply, RSP_FS2_RMDIR, CMD_FS2_RMDIR);
#endif
}

void handler_fs2_rename(const IocFrame *request, IocFrame *reply)
{
#if FF_FS_READONLY
    reply_init(request, reply, RSP_FS2_RENAME,
               IOC_STATUS_FS2_READ_ONLY, 0u);
#else
    char from[FS2_PATH_MAX + 1u];
    char to[FS2_PATH_MAX + 1u];
    FATFS *fs;
    uint8_t status = need_fs(&fs);
    FILINFO info;
    (void)fs;

    if ((status == IOC_STATUS_OK) &&
        (!make_path(from, &request->bytes[IOC_OFF_FS2_RENAME_FROM], false) ||
         !make_path(to, &request->bytes[IOC_OFF_FS2_RENAME_TO], false)))
        status = IOC_STATUS_FS2_BAD_NAME;
    /* f_rename reports FR_DENIED for an existing destination, which maps to
     * the read-only status and reads as a permission problem.  Say EXISTS. */
    if ((status == IOC_STATUS_OK) && (f_stat(to, &info) == FR_OK))
        status = IOC_STATUS_FS2_EXISTS;
    if (status == IOC_STATUS_OK) {
        close_all_files();
        status = map_result(f_rename(from, to));
    }
    reply_init(request, reply, RSP_FS2_RENAME, status, 0u);
#endif
}

void handler_fs2_sync(const IocFrame *request, IocFrame *reply)
{
#if FF_FS_READONLY
    reply_init(request, reply, RSP_FS2_SYNC,
               IOC_STATUS_FS2_READ_ONLY, 0u);
#else
    uint16_t token = get16(&request->bytes[IOC_OFF_FS2_TOKEN]);
    uint8_t status;
    Fs2File *file = file_for(token, &status);
    if ((status == IOC_STATUS_OK) && !file->writable)
        status = IOC_STATUS_FS2_READ_ONLY;
    if (status == IOC_STATUS_OK)
        status = map_result(f_sync(&file->fil));
    reply_init(request, reply, RSP_FS2_SYNC, status, 0u);
#endif
}

void handler_fs2_truncate(const IocFrame *request, IocFrame *reply)
{
#if FF_FS_READONLY
    reply_init(request, reply, RSP_FS2_TRUNCATE,
               IOC_STATUS_FS2_READ_ONLY, 0u);
#else
    uint16_t token = get16(&request->bytes[IOC_OFF_FS2_TOKEN]);
    uint32_t size = get32(&request->bytes[IOC_OFF_FS2_TRUNCATE_SIZE]);
    uint8_t status;
    Fs2File *file = file_for(token, &status);
    FRESULT fr;

    if ((status == IOC_STATUS_OK) && !file->writable)
        status = IOC_STATUS_FS2_READ_ONLY;
    if (status == IOC_STATUS_OK) {
        fr = f_lseek(&file->fil, (FSIZE_t)size);
        status = map_result(fr);
    }
    if (status == IOC_STATUS_OK) {
        fr = f_truncate(&file->fil);
        status = map_result(fr);
    }
    if (status == IOC_STATUS_OK)
        file->position = size;
    reply_init(request, reply, RSP_FS2_TRUNCATE, status, 0u);
#endif
}
