dumaiss/Zephyr-80/Code/HOST/CPM2.2/src/drivers/storage/sd.asm

; Zephyr-80 CP/M storage backend: SD card via the IO Controller, with a
; host-side 512-byte deblock line.
;
; Drives B: (unit 0) and C: (unit 1), two SD volumes on the one card, plus the
; dispatcher for the gated synthetic FAT BIOS D:.  The MCU
; owns an 8-slot LRU cache of 512-byte blocks but serves 128-byte CP/M records
; out of it -- CP/M's record is 128 bytes, the card's block is 512 -- so a
; sequential read was paying a whole IOCALL + READY + IOCBULK per quarter
; block.  The Z80 now keeps one 512-byte deblock line in bank 7
; (SD_DEBLOCK_BUFFER, CC00h) with its tag state at SD_DEBLOCK_TAG (CE00h):
; three reads in four are served from the line with no MCU transaction at all.
; One line on purpose, not a cache -- no replacement policy, no read-ahead, no
; dirty state; one line is all sequential CP/M access needs.
;
;   READ   record -> split into logical block + quarter.  A line hit copies
;                    the quarter straight to the caller's DMA.  A miss:
;                    CMD_SD_READ_BLOCK (0Fh), READY, 512 bytes on the bulk
;                    lane, volume-relative -- the same MCU volume mapping and
;                    the same MCU cache as CMD_SD_READ_REC.  0Fh is
;                    deliberately not the raw-LBA CMD_SD_READ_BULK, which is
;                    diagnostic-only and bypasses volume mapping.
;   WRITE  record -> CMD_SD_WRITE_REC, READY, 128 bytes out, then DONE.
;                    The line is read-side: after a write the MCU has
;                    accepted, the affected quarter is refreshed from the
;                    same DMA bytes when the line holds the containing block,
;                    and a failed write drops the line when the failure
;                    targeted that block.
;
; The record number is what the VDrip backend already computed as its LBA:
; track * 4 + sector, which for an 8 MiB volume is exactly a 16-bit quantity.
; The wire field is 32 bits so the protocol does not need widening later.
;
; WRITE always takes the DONE round trip.  Bytes reaching the MCU says nothing
; about whether they were stored: for a deferred write DONE reports whether the
; containing block could be read, and for the write-through block it reports the
; card's own status.  It is also the only thing that reports a bulk CRC failure.
;
; Scratch is MOVE_BUFFER, which is 192 bytes and divides exactly into the
; 128-byte record and the two 32-byte command frames.  Nothing else is live
; during a storage transaction -- CP/M does not re-enter the BIOS.
;
; The reply echo is compared against sd_deblock_echo, not sd_storage_record: a
; block request echoes the block it decoded and a record request the record, so
; one comparison serves both.
;
; SD_DEBLOCK_HITS / SD_DEBLOCK_MISSES are diagnostic and temporary; see
; docs/storage-profiling.md.

; Assembled as its own translation unit.  Areas are namespaced to it: asxxxx
; concatenates same-named areas across objects, which makes a following .org
; relative rather than absolute (tools/check_org_placement.py).
	.include "config.inc"
	.include "layout/platform.inc"
	.include "layout/memory.inc"

	.globl IOCALL
	.globl IOCBULK
	.globl IOCBULKW
	.globl SD_DEBLOCK_HITS,SD_DEBLOCK_MISSES
	.globl sd_storage_home,sd_storage_settrk
	.globl sd_storage_setsec,sd_storage_read,sd_storage_write
	.globl sd_storage_sectran,sd_storage_flush
	.globl stg_home,stg_seldsk,stg_settrk,stg_setsec
	.globl stg_read,stg_write,stg_sectran
	.globl stg_a_home,stg_a_seldsk,stg_a_seldsk_unsupported
	.globl stg_a_settrk,stg_a_setsec
	.globl stg_a_read,stg_a_write,stg_a_sectran
	.globl fat_bios_home,fat_bios_seldsk
	.globl fat_bios_settrk,fat_bios_setsec
	.globl fat_bios_read,fat_bios_write,fat_bios_sectran
	.globl storage_caller_sp
	.globl SD_STORAGE_CODE_START,SD_STORAGE_CODE_END
	.globl SD_PROBE_CODE_START,SD_PROBE_CODE_END
	.globl SD_PROBE2_CODE_END
	.globl cbios_dma_addr

	.area SDBK_CODE (ABS)
	.org CBIOS_STORAGE_SD_CODE_BASE

SD_STORAGE_CODE_START:

; ---------------------------------------------------------------------------
; CP/M entry points
; ---------------------------------------------------------------------------

sd_storage_home:
	ld hl,#0
	ld (sd_storage_track),hl
	ret

sd_storage_settrk:
	ld (sd_storage_track),bc
	ret

sd_storage_setsec:
	ld (sd_storage_sector),bc
	ret

sd_storage_sectran:
	ld h,b
	ld l,c
	ret

; ---------------------------------------------------------------------------
; record = track * 4 + sector
;
; Output: A = BIOS_OK and sd_storage_record set, or BIOS_ERR.
; The bounds check is not decoration: a wrapped record is a write to the wrong
; sector, which is the one failure that destroys data while reporting success.
; ---------------------------------------------------------------------------
sd_compute_record:
	ld hl,(sd_storage_track)
	ld a,h
	cp #0x40			; 16384 tracks
	jr nc,sd_record_bad
	ld de,(sd_storage_sector)
	ld a,d
	or a
	jr nz,sd_record_bad
	ld a,e
	cp #4				; 4 records per track
	jr nc,sd_record_bad
	add hl,hl
	add hl,hl
	ld d,#0
	add hl,de
	ld (sd_storage_record),hl
	xor a
	ret
sd_record_bad:
	ld a,#BIOS_ERR
	ret

; ---------------------------------------------------------------------------
; Frame helpers
; ---------------------------------------------------------------------------

; Zero both frames.
sd_zero_frames:
	ld hl,#(MOVE_BUFFER + SD_STORAGE_TX_OFF)
	ld b,#64			; tx and rx are adjacent
	xor a
sd_zf_loop:
	ld (hl),a
	inc hl
	djnz sd_zf_loop
	ret

; Build a record-addressed request.  In: A = command class.
sd_build_request:
	ld hl,#(MOVE_BUFFER + SD_STORAGE_TX_OFF)
	ld (hl),a			; class
	inc hl
	ld (hl),#0x01			; seq placeholder; IOCALL stamps the real one
	inc hl
	ld (hl),#0x00			; status
	inc hl
	ld (hl),#0x05			; payload: 32-bit record, then the unit
	inc hl
	ld de,(sd_storage_record)
	ld (hl),e
	inc hl
	ld (hl),d
	inc hl
	ld (hl),#0x00
	inc hl
	ld (hl),#0x00
	inc hl
	; The unit is sent EXPLICITLY, including B:'s zero.
	;
	; The controller reads this byte only when LEN is 5 or more and defaults
	; to unit 0 otherwise, so a length of 4 would still work -- but it would
	; mean B: relied on a compatibility fallback to address the right volume,
	; and a request whose meaning depends on what it omits is one edit away
	; from addressing the wrong disk.
	ld a,(sd_storage_unit)
	ld (hl),a
	ret

; Send the staged request and check the reply.
; In:  A = expected response class.
; Out: A = BIOS_OK, or BIOS_ERR / BIOS_ERR_BAD_REPLY.
sd_exchange:
	ld (sd_storage_expect),a
	ld hl,#(MOVE_BUFFER + SD_STORAGE_TX_OFF)
	ld de,#(MOVE_BUFFER + SD_STORAGE_RX_OFF)
	call IOCALL
	or a
	jr nz,sd_exchange_xport
	ld a,(MOVE_BUFFER + SD_STORAGE_RX_OFF)
	ld hl,#sd_storage_expect
	cp (hl)
	jr nz,sd_exchange_reply
	ld a,(MOVE_BUFFER + SD_STORAGE_RX_OFF + 2)
	or a
	jr nz,sd_exchange_status
	; The MCU echoes the record it decoded.  The frame CRC proves the frame
	; arrived intact; this proves both ends agree on what it MEANT, which a
	; decode bug on either side would survive.
	; sd_deblock_echo, not sd_storage_record: a block request echoes the block
	; it decoded, a record request the record.  One comparison serves both.
	ld hl,#(MOVE_BUFFER + SD_STORAGE_RX_OFF + 8)
	ld a,(sd_deblock_echo)
	cp (hl)
	jr nz,sd_exchange_echo
	inc hl
	ld a,(sd_deblock_echo + 1)
	cp (hl)
	jr nz,sd_exchange_echo
	xor a
	ret
sd_exchange_xport:
	ld a,#BIOS_ERR_TIMEOUT
	ret
sd_exchange_reply:
	ld a,#BIOS_ERR_BAD_REPLY
	ret
sd_exchange_status:
	ld a,#BIOS_ERR_IO
	ret
sd_exchange_echo:
	ld a,#BIOS_ERR_BAD_REPLY
	ret

; ---------------------------------------------------------------------------
; Record copies.  The BIOS runs in mode 11, where every address ZSDOS hands it is
; visible as it stands: its own directory buffer in bank 7, the facade's staging
; buffers in common memory, or the program's caller window.  So the copies need
; no bank selection.  They used to select DMA_BANK around the copy, back when
; the BIOS was common and could not see a program's buffers.
; ---------------------------------------------------------------------------

sd_copy_to_dma:
	ld hl,#(MOVE_BUFFER + SD_STORAGE_DATA_OFF)
	ld de,(cbios_dma_addr)
	ld bc,#SD_STORAGE_RECORD_BYTES
	ldir
	xor a
	ret

sd_copy_from_dma:
	ld hl,(cbios_dma_addr)
	ld de,#(MOVE_BUFFER + SD_STORAGE_DATA_OFF)
	ld bc,#SD_STORAGE_RECORD_BYTES
	ldir
	xor a
	ret

; ---------------------------------------------------------------------------
; READ one record
; ---------------------------------------------------------------------------
sd_storage_read:
	call sd_compute_record
	or a
	ret nz

	call sd_deblock_split
	call sd_deblock_match
	jr nz,sd_read_miss

	ld hl,#SD_DEBLOCK_HITS
	call sd_deblock_bump
	jr sd_read_serve
sd_read_miss:
	ld hl,#SD_DEBLOCK_MISSES
	call sd_deblock_bump
	call sd_deblock_fill
	or a
	ret nz
sd_read_serve:
	call sd_deblock_to_dma
	xor a
	ret

; ---------------------------------------------------------------------------
; Deblock helpers
; ---------------------------------------------------------------------------

; Split sd_storage_record into the logical block and the quarter within it.
; Out: sd_deblock_want = record >> 2, sd_deblock_quarter = record & 3.
sd_deblock_split:
	ld hl,(sd_storage_record)
	ld a,l
	and #(SD_STORAGE_RECS_PER_BLOCK - 1)
	ld (sd_deblock_quarter),a
	srl h
	rr l
	srl h
	rr l
	ld (sd_deblock_want),hl
	ret

; Z when the line is valid and holds the wanted unit and block.
sd_deblock_match:
	ld a,(sd_deblock_valid)
	or a
	jr z,sd_deblock_miss
	ld a,(sd_deblock_unit)
	ld hl,#sd_storage_unit
	cp (hl)
	ret nz
	ld hl,(sd_deblock_block)
	ld de,(sd_deblock_want)
	ld a,h
	cp d
	ret nz
	ld a,l
	cp e
	ret
sd_deblock_miss:
	or #0xff			; A non-zero: report NZ, never a false hit
	ret

; Bump the 16-bit counter at HL, saturating rather than wrapping: a wrapped
; count reads as a plausible small number, and the whole point is the ratio.
; Diagnostic; remove with the counters.
sd_deblock_bump:
	inc (hl)
	ret nz
	inc hl
	inc (hl)
	ret nz
	ld (hl),#0xff			; both bytes rolled: pin at FFFF
	dec hl
	ld (hl),#0xff
	ret

; Drop the line.  Cheap enough to call on any path that could make it stale.
sd_deblock_invalidate:
	xor a
	ld (sd_deblock_valid),a
	ret

; Fetch one logical 512-byte block into the line.
;
; The line is invalidated FIRST and marked valid only after the whole
; transaction has succeeded, so any failure -- transport, wrong class, MCU
; status, echo mismatch, short READY, bulk error -- leaves it invalid rather
; than holding a partially filled block that would then be served as data.
; Out: A = BIOS_OK, or a BIOS_ERR_* code.
sd_deblock_fill:
	call sd_deblock_invalidate

	call sd_zero_frames
	ld a,#SD_CMD_READ_BLOCK
	call sd_build_block_request
	ld hl,(sd_deblock_want)
	ld (sd_deblock_echo),hl
	ld a,#SD_RSP_READ_BLOCK
	call sd_exchange
	or a
	ret nz

	; READY must promise exactly one block.  The record path can accept the
	; MCU's declared length because a short record is still a whole answer;
	; here a short block would leave three quarters of the line undefined and
	; every one of them would later be served as data.
	ld a,(MOVE_BUFFER + SD_STORAGE_RX_OFF + 6)
	cp #0x00			; 512 low
	jr nz,sd_deblock_bad_len
	ld a,(MOVE_BUFFER + SD_STORAGE_RX_OFF + 7)
	cp #0x02			; 512 high
	jr nz,sd_deblock_bad_len

	; Straight into the line: mode 11 has bank 7 addressable, so no staging
	; buffer and no second copy.
	ld hl,#SD_DEBLOCK_BUFFER
	ld de,#SD_STORAGE_BLOCK_BYTES
	call IOCBULK
	or a
	jr nz,sd_deblock_bulk_failed

	; Only now is the line real.
	ld hl,(sd_deblock_want)
	ld (sd_deblock_block),hl
	ld a,(sd_storage_unit)
	ld (sd_deblock_unit),a
	ld a,#1
	ld (sd_deblock_valid),a
	xor a
	ret
sd_deblock_bad_len:
	ld a,#BIOS_ERR_BAD_REPLY
	ret
sd_deblock_bulk_failed:
	ld a,#BIOS_ERR_IO
	ret

; HL = the wanted quarter inside the line.
sd_deblock_quarter_addr:
	ld a,(sd_deblock_quarter)
	ld h,#0
	ld l,a
	add hl,hl
	add hl,hl
	add hl,hl
	add hl,hl
	add hl,hl
	add hl,hl
	add hl,hl			; quarter * 128
	ld de,#SD_DEBLOCK_BUFFER
	add hl,de
	ret

; Serve the selected 128-byte quarter to the caller's DMA address.
sd_deblock_to_dma:
	call sd_deblock_quarter_addr
	ld de,(cbios_dma_addr)
	ld bc,#SD_STORAGE_RECORD_BYTES
	ldir
	xor a
	ret

; Refresh the selected quarter from the caller's DMA address, after a write the
; MCU has accepted.  Keeps the line coherent without making it dirty: the
; controller remains the only thing that owns write-back.
sd_deblock_from_dma:
	call sd_deblock_quarter_addr
	ex de,hl
	ld hl,(cbios_dma_addr)
	ld bc,#SD_STORAGE_RECORD_BYTES
	ldir
	ret

; Build a block-addressed request.  In: A = command class.
sd_build_block_request:
	ld hl,#(MOVE_BUFFER + SD_STORAGE_TX_OFF)
	ld (hl),a			; class
	inc hl
	ld (hl),#0x01			; seq placeholder; IOCALL stamps the real one
	inc hl
	ld (hl),#0x00			; status
	inc hl
	ld (hl),#0x05			; payload: 32-bit block, then the unit
	inc hl
	ld de,(sd_deblock_want)
	ld (hl),e
	inc hl
	ld (hl),d
	inc hl
	ld (hl),#0x00
	inc hl
	ld (hl),#0x00
	inc hl
	ld a,(sd_storage_unit)
	ld (hl),a
	ret

; ---------------------------------------------------------------------------
; WRITE one record
;
; C holds CP/M's write type on entry and is deliberately ignored.  The deferral
; policy lives on the MCU and is an address rule there -- the block holding the
; directory head is write-through, everything else rides the flush timer -- so
; the controller never has to know what a directory is.
; ---------------------------------------------------------------------------
sd_storage_write:
	call sd_compute_record
	or a
	ret nz

	call sd_copy_from_dma

	call sd_zero_frames
	ld a,#SD_CMD_WRITE_REC
	call sd_build_request
	ld hl,(sd_storage_record)
	ld (sd_deblock_echo),hl
	ld a,#SD_RSP_WRITE_REC
	call sd_exchange
	or a
	ret nz

	ld hl,#(MOVE_BUFFER + SD_STORAGE_DATA_OFF)
	ld de,#SD_STORAGE_RECORD_BYTES
	call IOCBULKW
	or a
	jr nz,sd_write_bulk_failed

	; DONE is mandatory and has no fast path.
	call sd_zero_frames
	ld hl,#(MOVE_BUFFER + SD_STORAGE_TX_OFF)
	ld (hl),#SD_CMD_XFER_STATUS
	inc hl
	ld (hl),#0x01
	ld a,#SD_RSP_XFER_STATUS
	ld (sd_storage_expect),a
	ld hl,#(MOVE_BUFFER + SD_STORAGE_TX_OFF)
	ld de,#(MOVE_BUFFER + SD_STORAGE_RX_OFF)
	call IOCALL
	or a
	jr nz,sd_write_xport_failed
	ld a,(MOVE_BUFFER + SD_STORAGE_RX_OFF)
	cp #SD_RSP_XFER_STATUS
	jr nz,sd_write_reply_failed
	ld a,(MOVE_BUFFER + SD_STORAGE_RX_OFF + 5)
	or a
	jr nz,sd_write_done_failed

	; The controller has accepted the record.  If the line happens to hold the
	; block it landed in, refresh that quarter from the same DMA bytes that
	; were just sent, so a read-after-write cannot be served stale data.
	;
	; This does NOT make the line dirty: the bytes are already with the
	; controller, which remains the only thing that owns write-back.  The DMA
	; address is still the caller's and still addressable -- the write path
	; read from it a few instructions ago through sd_copy_from_dma.
	call sd_deblock_split
	call sd_deblock_match
	jr nz,sd_write_ok
	call sd_deblock_from_dma
sd_write_ok:
	xor a
	ret
sd_write_bulk_failed:
	call sd_deblock_drop_if_cached
	ld a,#BIOS_ERR_IO
	ret

; A write that failed may or may not have disturbed the block; the line cannot
; tell which, so it drops the line when the failure targeted the cached block.
; Conservative on purpose: correctness over keeping the line.
sd_deblock_drop_if_cached:
	push af
	call sd_deblock_split
	call sd_deblock_match
	jr nz,sd_deblock_drop_done
	call sd_deblock_invalidate
sd_deblock_drop_done:
	pop af
	ret
sd_write_xport_failed:
	call sd_deblock_drop_if_cached
	ld a,#BIOS_ERR_TIMEOUT
	ret
sd_write_reply_failed:
	call sd_deblock_drop_if_cached
	ld a,#BIOS_ERR_BAD_REPLY
	ret
sd_write_done_failed:
	call sd_deblock_drop_if_cached
	ld a,#BIOS_ERR_IO
	ret

; ---------------------------------------------------------------------------
; Commit every dirty cache slot.  No bulk phase: the reply status IS the answer,
; which makes this the one storage command whose result needs no DONE query.
; ---------------------------------------------------------------------------
sd_storage_flush:
	call sd_zero_frames
	ld hl,#(MOVE_BUFFER + SD_STORAGE_TX_OFF)
	ld (hl),#SD_CMD_FLUSH
	inc hl
	ld (hl),#0x01
	ld hl,#(MOVE_BUFFER + SD_STORAGE_TX_OFF)
	ld de,#(MOVE_BUFFER + SD_STORAGE_RX_OFF)
	call IOCALL
	or a
	jr nz,sd_flush_failed
	ld a,(MOVE_BUFFER + SD_STORAGE_RX_OFF)
	cp #SD_RSP_FLUSH
	jr nz,sd_flush_failed
	ld a,(MOVE_BUFFER + SD_STORAGE_RX_OFF + 2)
	or a
	jr nz,sd_flush_failed
	xor a
	ret
sd_flush_failed:
	ld a,#BIOS_ERR_IO
	ret

; ---------------------------------------------------------------------------
; Drive dispatcher
;
; SELDSK records which backend is live; everything after it routes among the
; drive-A backend, SD volumes, and the synthetic FAT BIOS on that state.
; CP/M always calls SELDSK before the SETTRK/SETSEC/READ/WRITE that act on a
; drive, so a single "active backend" byte is sufficient and is how ordinary
; multi-drive BIOSes do it.
;
; An unsupported drive parks stg_drive at FFh so a stray READ that arrives
; without a preceding SELDSK fails rather than silently addressing A:.
; ---------------------------------------------------------------------------



stg_home:
	call stg_is_fat
	jp z,fat_bios_home
	call stg_is_sd
	jp z,sd_storage_home
	push hl
	call stg_a_home
	pop hl
	ret

stg_settrk:
	call stg_is_fat
	jp z,fat_bios_settrk
	call stg_is_sd
	jp z,sd_storage_settrk
	jp stg_a_settrk

stg_setsec:
	call stg_is_fat
	jp z,fat_bios_setsec
	call stg_is_sd
	jp z,sd_storage_setsec
	jp stg_a_setsec

stg_sectran:
	call stg_is_fat
	jp z,fat_bios_sectran
	call stg_is_sd
	jp z,sd_storage_sectran
	jp stg_a_sectran

; READ and WRITE run on the BIOS stack.
;
; CP/M's BDOS calls disk I/O on a small private stack, and both backends nest
; well past what it allows -- frame build, transport, bulk loop, bank switch.
; The caller's stack is restored before returning.
stg_read:
	push bc
	push de
	push hl
	call stg_is_fat
	ld hl,#fat_bios_read
	jr z,stg_run
	call stg_is_sd
	ld hl,#sd_storage_read
	jr z,stg_run
	ld hl,#stg_a_read
	jr stg_run

stg_write:
	push bc
	push de
	push hl
	call stg_is_fat
	ld hl,#fat_bios_write
	jr z,stg_run
	call stg_is_sd
	ld hl,#sd_storage_write
	jr z,stg_run
	ld hl,#stg_a_write

stg_run:
	ld (storage_caller_sp),sp
	ld sp,#CBIOS_CONSOLE_STACK_TOP
	ld de,#stg_run_return
	push de
	jp (hl)
stg_run_return:
	ld hl,(storage_caller_sp)
	ld sp,hl
	pop hl
	pop de
	pop bc
	ret

SD_STORAGE_CODE_END:

; ---------------------------------------------------------------------------
; Disk parameter header and block for B:.
;
; The directory buffer is shared with A:, which is ordinary CP/M -- one DIRBUF
; serves every DPH.  The DPB is NOT shared.  It used to point at the A: backend's
; DPB, which was correct only while A: was the VDrip proxy volume, because that
; volume and this card have the same 8 MiB geometry.  A: is now a 144 KiB ROM
; disk by default, so B: carries its own DPB or it would be described by the
; wrong geometry entirely.
;
; CSV is empty because CKS is zero -- a fixed disk that CP/M never re-verifies.
; ---------------------------------------------------------------------------
	.area SDBK_CODE (ABS)
	.org SD_STORAGE_DPH
SD_STORAGE_DPH_DATA:
	.dw 0x0000			; XLT: no skew table
	.dw 0x0000
	.dw 0x0000
	.dw 0x0000
	.dw CBIOS_STORAGE_DIRBUF	; shared with A:
	.dw SD_STORAGE_DPB		; private: 8 MiB card geometry
	.dw 0x0000			; CSV: CKS = 0
	.dw SD_STORAGE_ALV_BUFFER

; CP/M Drive Parameter Block for the SD volume:
;   SPT=4, BSH=5, BLM=31, EXM=1, DSM=2047, DRM=511, AL0=F0h, AL1=00h,
;   CKS=0, OFF=0.  Occupies the last 16 bytes of the DPH/DPB window.
	.area SDBK_CODE (ABS)
	.org SD_STORAGE_DPB
SD_STORAGE_DPB_DATA:
	.dw SD_STORAGE_SECTORS_PER_TRACK
	.db SD_STORAGE_BLOCK_SHIFT
	.db SD_STORAGE_BLOCK_MASK
	.db SD_STORAGE_EXTENT_MASK
	.dw SD_STORAGE_MAX_BLOCK
	.dw SD_STORAGE_DIR_ENTRIES
	.db SD_STORAGE_ALLOC0
	.db SD_STORAGE_ALLOC1
	.dw SD_STORAGE_CHECK_SIZE
	.dw SD_STORAGE_OFFSET_TRACKS

; ---------------------------------------------------------------------------
; C: -- the second SD volume.
;
; Same geometry as B:, so it shares SD_STORAGE_DPB, and the same shared DIRBUF
; every DPH uses.  CSV is empty because CKS is zero.  The allocation vector is
; the only thing CP/M will not let two drives share, and it is why a third drive
; costs 272 bytes rather than 16.
; ---------------------------------------------------------------------------
	.area SDBK_CODE (ABS)
	.org SD_STORAGE_DPH2
SD_STORAGE_DPH2_DATA:
	.dw 0x0000			; XLT: no skew table
	.dw 0x0000
	.dw 0x0000
	.dw 0x0000
	.dw CBIOS_STORAGE_DIRBUF	; shared with A: and B:
	.dw SD_STORAGE_DPB		; shared with B:: identical 8 MiB geometry
	.dw 0x0000			; CSV: CKS = 0
	.dw SD_STORAGE_ALV2_BUFFER

; C:'s allocation vector, RESERVED not merely addressed.
;
; Without this .blkb the 256 bytes are invisible to the layout tools: the
; headroom table in docs/memory-map.md listed F980h-FA7Fh as free slot-5 space
; while C:'s DPH was already pointing at it.  The next component placed there
; would have been handed CP/M's live allocation bitmap to overwrite -- and
; nothing would have reported it, because check_overlap.py only sees bytes that
; are emitted or reserved.
	.area SDBK_WORK (ABS)
	.org SD_STORAGE_ALV2_BUFFER
SD_STORAGE_ALV2:
	.ds SD_STORAGE_ALV2_SIZE

; ---------------------------------------------------------------------------
; ---------------------------------------------------------------------------
; SD selection probe.
;
; One linear routine.  It used to be four fragments -- request at F41Bh,
; recovery at DFEDh in the core BIOS tail, success at F909h and the result store
; at FA74h -- wedged into whatever gaps existed when each piece was written, and
; stitched together with jp instructions.  Nothing about the behaviour required
; that; only the absence of 41 contiguous bytes did.  Slot 5 has them now.
;
; The behaviour is unchanged and deliberately so: this is normal failure
; handling.  A failed transport or MCU status returns a zero DPH, BDOS applies
; its usual disk-error policy, and the machine warm-boots to A: instead of
; looping on a drive that will never answer.
;
; stg_run saved the caller's HL at storage_caller_sp; the paths below select the
; DPH value its return shim will restore.
;
; Inputs: none.  Output: the protected SELDSK caller receives the B: DPH in HL
; on success, or HL = 0 on failure.  Clobbers AF/BC/DE/HL.  May block for card
; initialization and IOCALL; emits IOC Command traffic, no Virtual Drip traffic.
; Foreground only: uses MOVE_BUFFER and is not ISR-safe.
; ---------------------------------------------------------------------------
	.area SDBK_CODE (ABS)
; ---------------------------------------------------------------------------
; Deblock line and its tag, placed into the bank 7 image
; ---------------------------------------------------------------------------
;
; The line itself is reserved rather than emitted -- nothing may read it until
; a fill has succeeded, and the valid byte below is what enforces that.
; Reserving it here is what makes a later allocation at CC00h collide at build
; time instead of quietly sharing the address.
	.area SDBK_CODE (ABS)
	.org SD_DEBLOCK_BUFFER
SD_DEBLOCK_BUFFER_START:
	; EMITTED, not reserved.  check_overlap.py compares emitted bytes, so a
	; .ds here would occupy the address without defending it: a later region
	; .org'd into CC00h would assemble clean and silently share the line.
	; The bank is a full 64 KiB page either way, so the zeros cost nothing.
	.rept SD_DEBLOCK_BUFFER_SIZE
	.db 0
	.endm
SD_DEBLOCK_BUFFER_IMAGE_END:

; THE TAG IS EXPLICIT ZEROS, NOT .ds.
;
; Cold boot installs the full 64 KiB bank 7 page from ROM, and the unallocated
; fill is FFh.  A .ds here would leave sd_deblock_valid reading FFh on the first
; read after power-on: the line would report a hit, and 512 bytes of ROM fill
; would be served to CP/M as disk data.  The IOC failure record's reserved bytes
; are explicit zeros for the same reason.
	.area SDBK_CODE (ABS)
	.org SD_DEBLOCK_TAG
SD_DEBLOCK_TAG_START:
	.db 0				; sd_deblock_valid  -- invalid at cold boot
	.db 0				; sd_deblock_unit
	.dw 0				; sd_deblock_block
	.dw 0				; sd_deblock_want
	.db 0				; sd_deblock_quarter
	.dw 0				; sd_deblock_echo
SD_DEBLOCK_TAG_IMAGE_END:

	.area SDBK_CODE (ABS)
	.org CBIOS_SD_PROBE_CODE_BASE

SD_PROBE_CODE_START:
sd_storage_probe:
	call sd_storage_probe_card
	jr nz,sd_probe_failed
	ld de,#SD_STORAGE_DPH
	jr sd_probe_store_result

sd_probe_failed:
	; The card did not answer.  Whatever the line holds came from a card that
	; may now be a different one, so drop it -- this is the media event the
	; unit/block tag cannot cover.  Only on FAILURE: invalidating on every
	; successful probe would drop the line on each SELDSK, and CP/M selects a
	; drive before essentially every BDOS file operation.
	call sd_deblock_invalidate
	ld de,#0x0000			; no DPH: drive unavailable
; In: DE = DPH to return, or zero for an unavailable drive.
; Out: saved SELDSK HL replaced with DE.  Clobbers HL; foreground only.
sd_probe_store_result:
	ld hl,(storage_caller_sp)
	ld (hl),e
	inc hl
	ld (hl),d
	ret
SD_PROBE_CODE_END:

; ---------------------------------------------------------------------------
; C: selection probe, in its own region.
; ---------------------------------------------------------------------------
	.area SDBK_CODE (ABS)
	.org CBIOS_SD_PROBE2_CODE_BASE
stg_seldsk:
	ld a,c
	cp #STORAGE_A_DRIVE
	jp z,stg_sel_a
	cp #FAT_BIOS_DRIVE
	jr z,stg_sel_fat
	; The remaining supported drives are SD volumes, and the unit each
	; addresses is the drive letter minus SD_STORAGE_DRIVE: C: -> 0, D: -> 1.
	; A: and B: were handled above and never enter this range.
	cp #SD_STORAGE_DRIVE
	jr c,stg_sel_bad
	cp #SD_STORAGE_DRIVE_LIMIT
	jr nc,stg_sel_bad
	ld (stg_drive),a
	sub #SD_STORAGE_DRIVE
	ld (sd_storage_unit),a
	push bc
	push de
	push hl
	or a				; unit 0 is C:
	jr z,stg_sel_unit0
	ld hl,#sd_storage_probe2
	jp stg_run
stg_sel_unit0:
	ld hl,#sd_storage_probe
	jp stg_run
stg_sel_bad:
	ld a,#0xff
	ld (stg_drive),a
	jp stg_a_seldsk_unsupported
stg_sel_fat:
	; The complete FAT personality is linked in every build.  The gate is
	; retained only for the recovery image that deliberately parks B:.
	ld a,#FAT_DRIVE_ENABLED
	or a
	jr z,stg_sel_bad
	ld a,#FAT_BIOS_DRIVE
	ld (stg_drive),a
	jp fat_bios_seldsk
stg_sel_a:
	ld a,#STORAGE_A_DRIVE
	ld (stg_drive),a
	jp stg_a_seldsk

; Z set when the SD backend is the live one -- for ANY of its drives.
;
; This used to compare against SD_STORAGE_DRIVE alone, which was the same thing
; while B: was the only SD volume.  With C: it is not: the routines that gate on
; it would have routed C:'s reads to the A: backend.
stg_is_sd:
	ld a,(stg_drive)
	cp #SD_STORAGE_DRIVE
	jr c,stg_not_sd			; below B: -- A:, or nothing selected
	cp #SD_STORAGE_DRIVE_LIMIT
	jr nc,stg_not_sd		; above the last SD drive, incl. the FFh park
	xor a				; Z set: an SD drive is live
	ret
stg_not_sd:
	; A: is drive 0, so `or a` would set Z here and route A: to the SD
	; backend.  The flag is set from a constant instead.
	ld a,#0xff
	or a				; NZ
	ret

; Z set when the synthetic FAT BIOS personality is the live backend.
stg_is_fat:
	ld a,(stg_drive)
	cp #FAT_BIOS_DRIVE
	ret

; Card-level probe, shared by B: and C:.  Out: Z when the card answered.
sd_storage_probe_card:
	call sd_zero_frames
	ld a,#SD_CMD_PROBE
	ld (MOVE_BUFFER + SD_STORAGE_TX_OFF),a
	ld hl,#(MOVE_BUFFER + SD_STORAGE_TX_OFF)
	ld de,#(MOVE_BUFFER + SD_STORAGE_RX_OFF)
	call IOCALL
	or a				; transport status
	ret nz
	ld a,(MOVE_BUFFER + SD_STORAGE_RX_OFF + IOC_OFF_STATUS)
	or a
	ret

; ---------------------------------------------------------------------------
; C: selection probe.
;
; Two transactions, and the order matters.
;
; The card probe runs first because it is what INITIALISES the card.  Only once
; the card is up does the controller's idle loop resolve /CPM/CPM_1.DRV and
; CPM_2.DRV into volume units -- so asking about unit 1 before that would
; truthfully answer "nothing mounted" on a perfectly good card.  The two IOCALLs
; are separate transactions, so the controller's main loop runs between them and
; the mount has happened by the time the second one is answered.
;
; CMD_VOL_INFO is then a pure query: no card I/O, no state change.  A mode of
; zero means unit 1 has no volume -- an unformatted card, or one with no
; CPM_2.DRV on it -- and C: reports itself unavailable, which is a clean select
; error rather than reads that fail one at a time later.
; ---------------------------------------------------------------------------
sd_storage_probe2:
	call sd_storage_probe_card
	jp nz,sd_probe_failed
	call sd_zero_frames
	ld a,#SD_CMD_VOL_INFO
	ld (MOVE_BUFFER + SD_STORAGE_TX_OFF),a
	ld a,#0x01
	ld (MOVE_BUFFER + SD_STORAGE_TX_OFF + IOC_OFF_LEN),a
	ld a,(sd_storage_unit)
	ld (MOVE_BUFFER + SD_STORAGE_TX_OFF + IOC_OFF_PAYLOAD),a
	ld hl,#(MOVE_BUFFER + SD_STORAGE_TX_OFF)
	ld de,#(MOVE_BUFFER + SD_STORAGE_RX_OFF)
	call IOCALL
	or a
	jp nz,sd_probe_failed
	ld a,(MOVE_BUFFER + SD_STORAGE_RX_OFF + IOC_OFF_STATUS)
	or a
	jp nz,sd_probe_failed
	ld a,(MOVE_BUFFER + SD_STORAGE_RX_OFF + SD_VOL_INFO_MODE_OFF)
	cp #SD_VOL_MODE_NONE
	jp z,sd_probe_failed		; unit exists, but nothing is mounted on it
	ld de,#SD_STORAGE_DPH2
	jp sd_probe_store_result

; The region ends at CBIOS_SD_PROBE2_CODE_END (F96Fh); SD_STORAGE_DPH2 is
; org'd immediately after it, so overrunning this block collides with C:'s own
; DPH and tools/check_overlap.py reports it by name.
SD_PROBE2_CODE_END:
